adysanchez-10/Grupo-4-oficial/Documentacion/Talleres/Taller 22.10.25/Ejemplo 3/Laminado de objetos.pdf

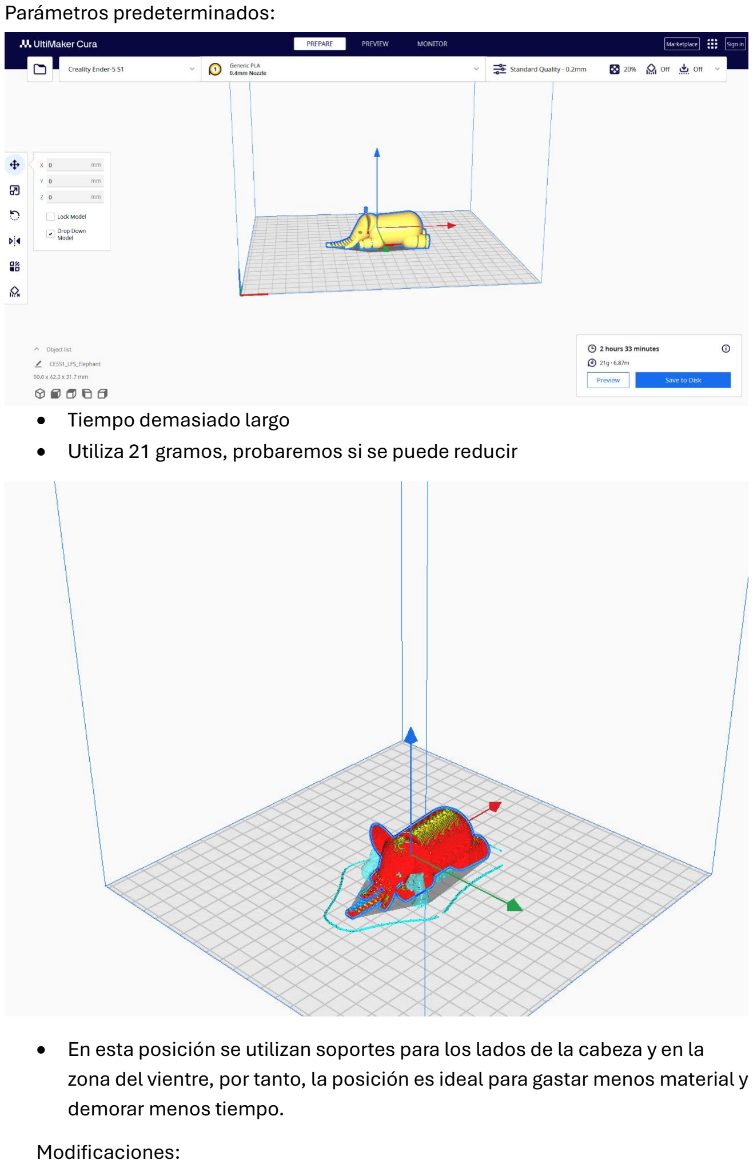
[picture p42: page 1]

Parámetros predeterminados:

- Tiempo demasiado largo
- Utiliza 21 gramos, probaremos si se puede reducir
- En esta posición se utilizan soportes para los lados de la cabeza y en la zona del vientre, por tanto, la posición es ideal para gastar menos material y demorar menos tiempo.
Modificaciones:

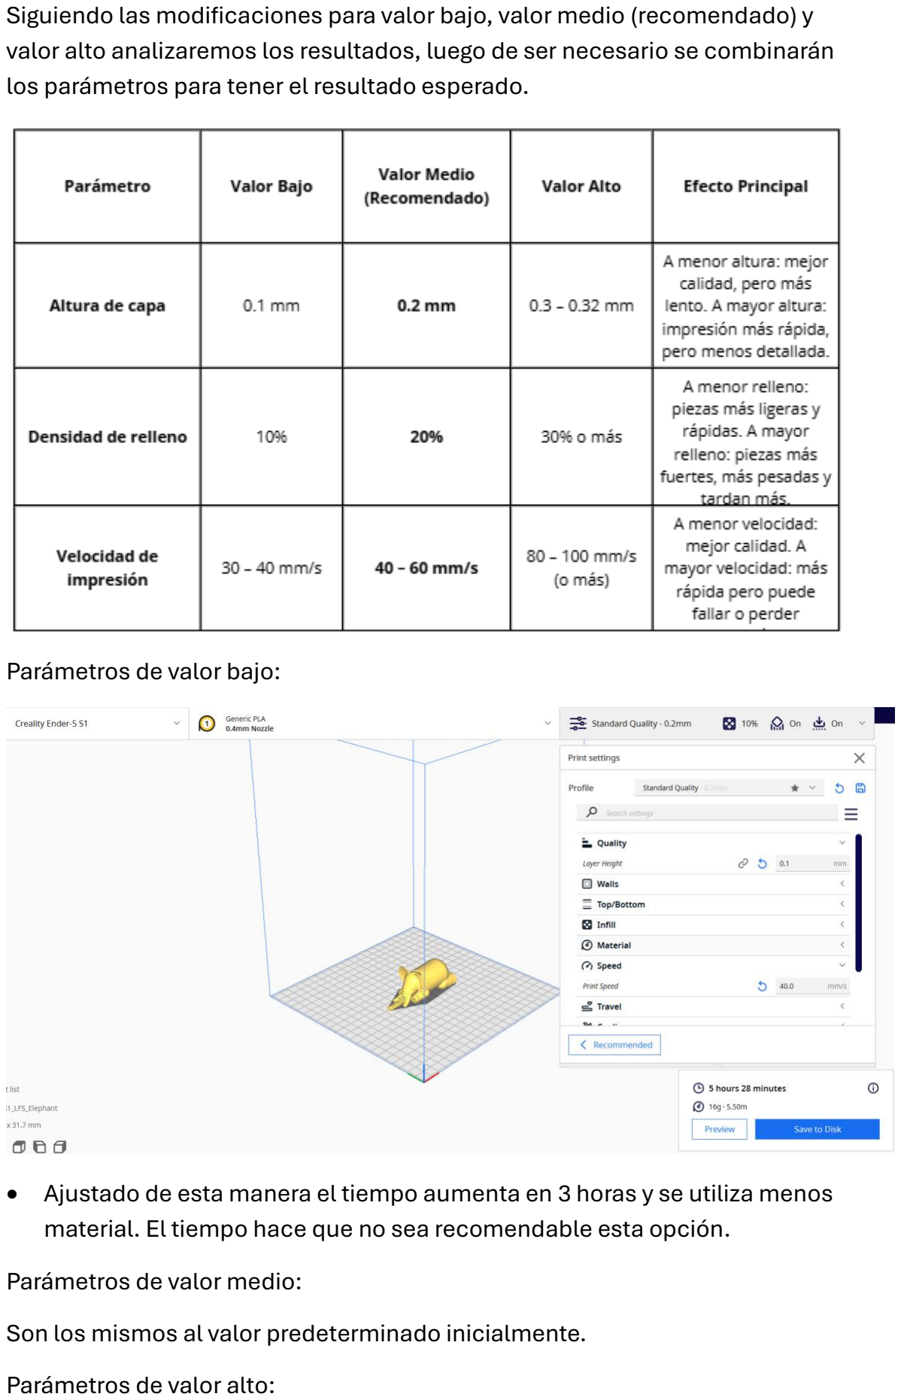
[picture p43: page 2]

Siguiendo las modificaciones para valor bajo, valor medio (recomendado) y valor alto analizaremos los resultados, luego de ser necesario se combinarán los parámetros para tener el resultado esperado.

Parámetros de valor bajo:

- Ajustado de esta manera el tiempo aumenta en 3 horas y se utiliza menos material. El tiempo hace que no sea recomendable esta opción. Parámetros de valor medio:
Son los mismos al valor predeterminado inicialmente.
Parámetros de valor alto:

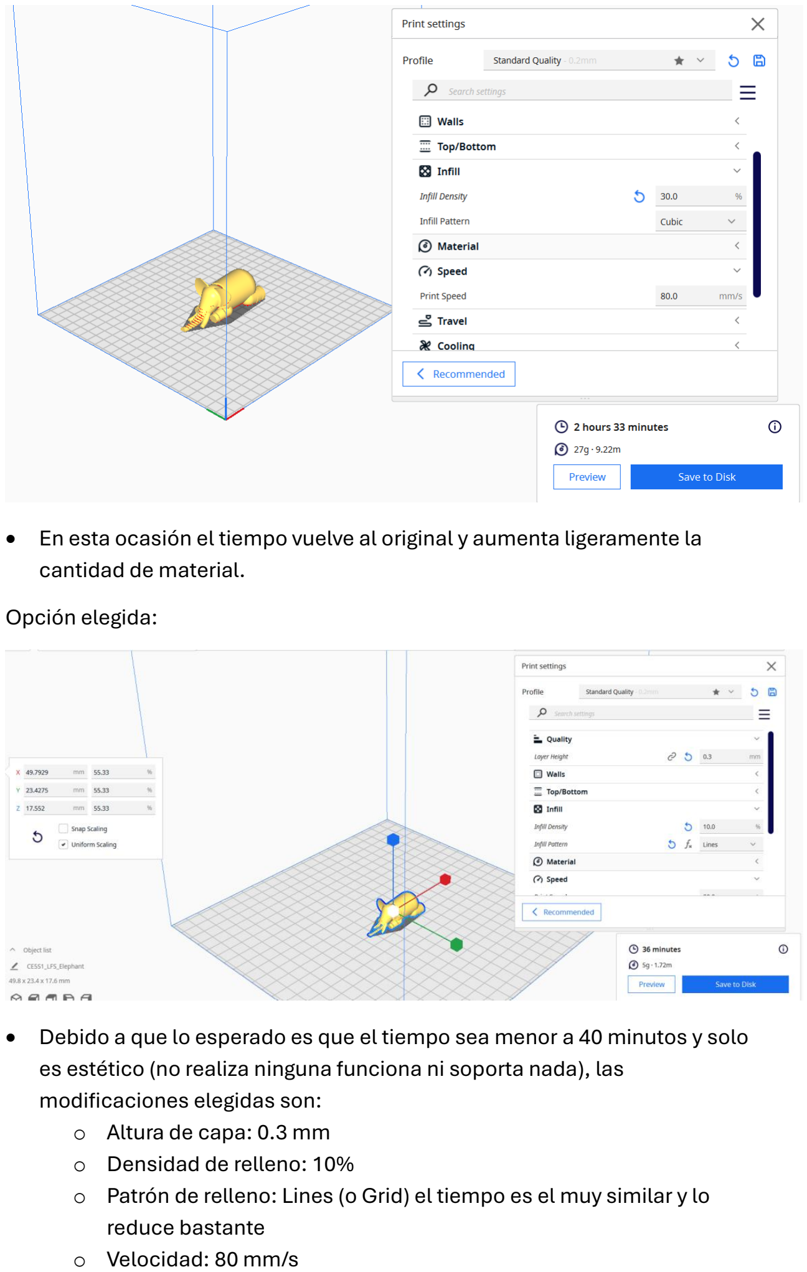
[picture p44: page 3]

- En esta ocasión el tiempo vuelve al original y aumenta ligeramente la cantidad de material.
Opción elegida:
- Debido a que lo esperado es que el tiempo sea menor a 40 minutos y solo es estético (no realiza ninguna funciona ni soporta nada), las modificaciones elegidas son:
- Altura de capa: 0.3 mm
- Densidad de relleno: 10%
- Patrón de relleno: Lines (o Grid) el tiempo es el muy similar y lo reduce bastante
- Velocidad: 80 mm/s

- Reducción de medidas: 49.8x23.4x17.6 mm (necesario para reducir el tiempo)
