adysanchez-10/Grupo-4-oficial/Documentacion/Entregables/Entregables corregidos/Entregable 8/ENTREGABLE 8 FUNBIO (1) (1).pdf

"Año de la recuperación y consolidación de la economía peruana"

## Universidad Peruana Cayetano Heredia - Pontificia Universidad Católica del Perú


## Facultad De Ciencias E Ingeniería Ingeniería Biomédica

Octavo entregable
“Diseño esquemático y modelado 3D”

Integrantes:
Rodriguéz Solano, Milagros Mariajosé Romaní León, Leonardo
Romero Guerrero, Gabriel
Salas Cano, Rodrigo Emiliano Sánchez Guevara, Ady Sebastián Seijas Rojas, Camila Andrea

Cuarto ciclo
Profesores:
Miguel Rogger Hoyos Alvitez Marco Mugaburu Celi
Shirley Pahuachon Nuñez
Fecha de entrega: 21/10/2025

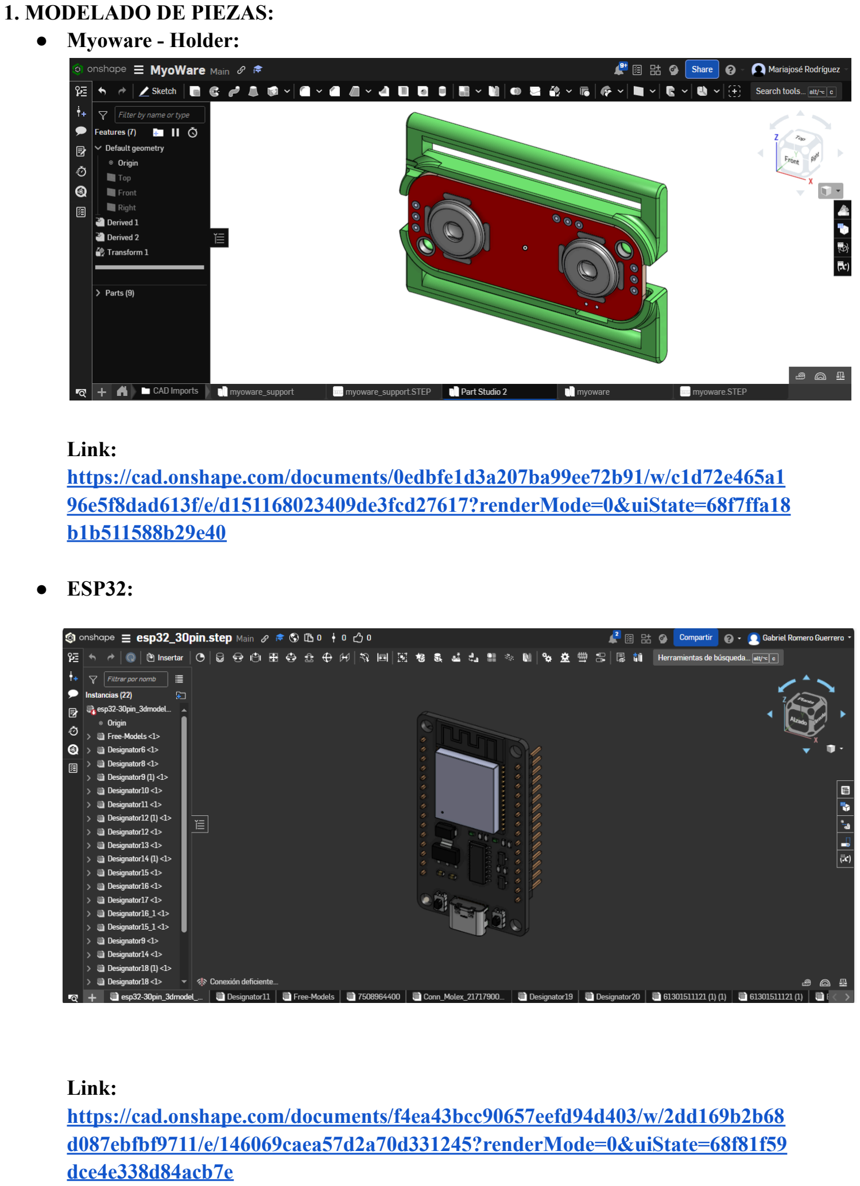
[picture p45: page 2]

### 1. MODELADO DE PIEZAS:

- Myoware - Holder:

Link:
https://cad.onshape.com/documents/0edbfe1d3a207ba99ee72b91/w/c1d72e465a196e5f8dad613f/e/d151168023409de3fcd27617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 b1b511588b29e40 (https://cad.onshape.com/documents/0edbfe1d3a207ba99ee72b91/w/c1d72e465a196e5f8dad613f/e/d151168023409de3fcd27617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)
- ESP32:

Link:
https://cad.onshape.com/documents/f4ea43bcc90657eefd94d403/w/2dd169b2b68d087ebfbf9711/e/146069caea57d2a70d331245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 dce4e338d84acb7e (https://cad.onshape.com/documents/f4ea43bcc90657eefd94d403/w/2dd169b2b68d087ebfbf9711/e/146069caea57d2a70d331245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)

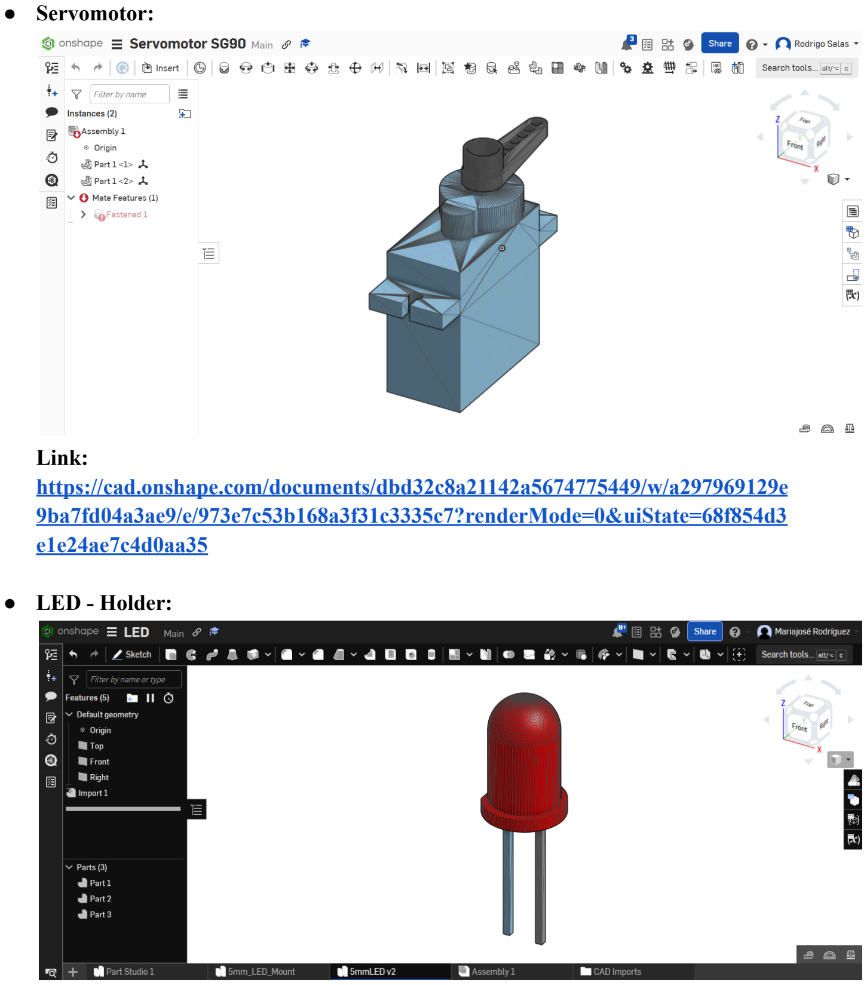
[picture p46: page 3]

- Servomotor:

Link:
https://cad.onshape.com/documents/dbd32c8a21142a5674775449/w/a297969129e9ba7fd04a3ae9/e/973e7c53b168a3f31c3335c7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 e1e24ae7c4d0aa35 (https://cad.onshape.com/documents/dbd32c8a21142a5674775449/w/a297969129e9ba7fd04a3ae9/e/973e7c53b168a3f31c3335c7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)
- LED - Holder:

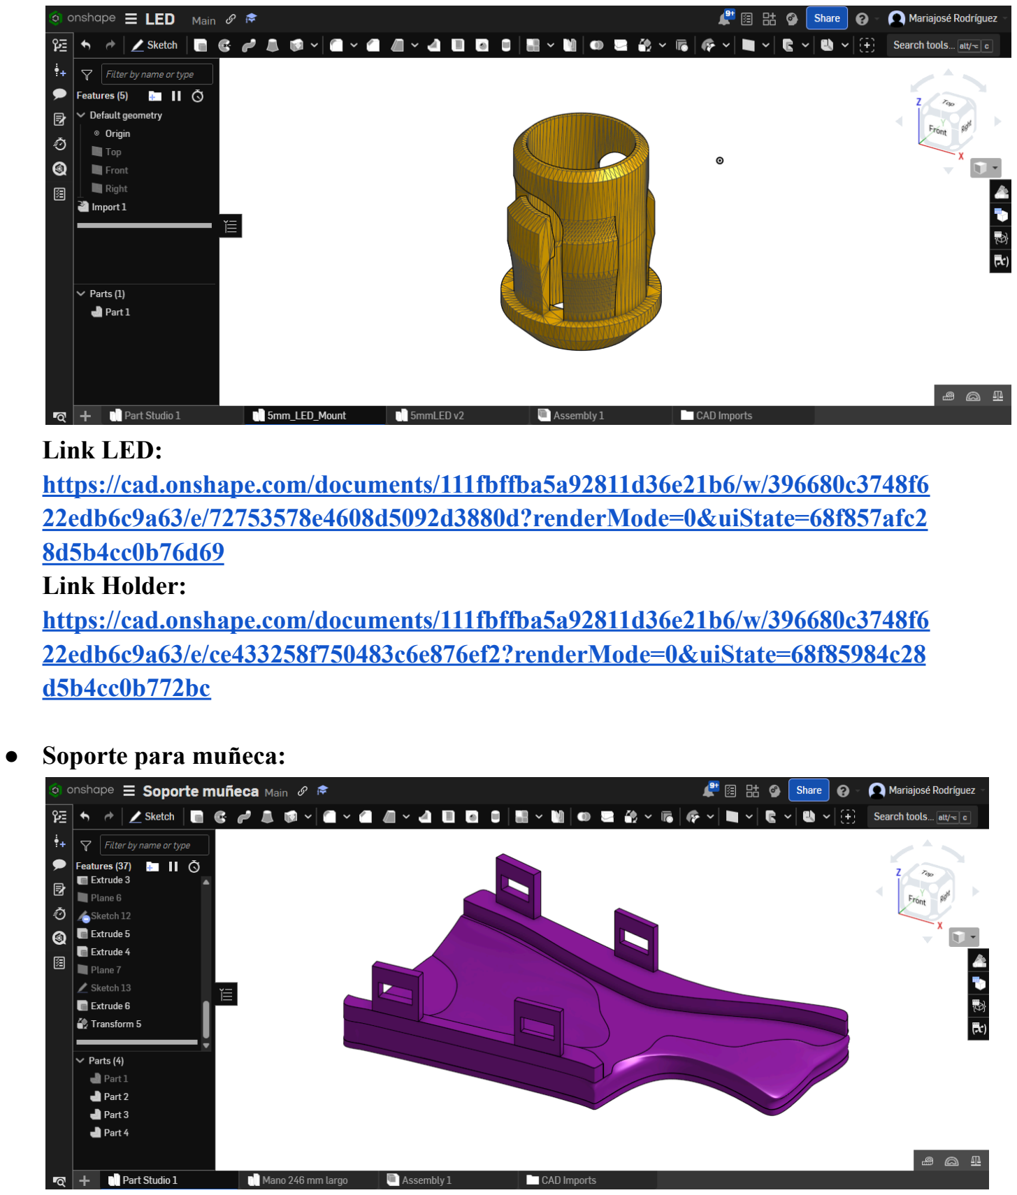
[picture p47: page 4]

Link LED:
https://cad.onshape.com/documents/111fbffba5a92811d36e21b6/w/396680c3748f622edb6c9a63/e/72753578e4608d5092d3880d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 8d5b4cc0b76d69 (https://cad.onshape.com/documents/111fbffba5a92811d36e21b6/w/396680c3748f622edb6c9a63/e/72753578e4608d5092d3880d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)
Link Holder:
https://cad.onshape.com/documents/111fbffba5a92811d36e21b6/w/396680c3748f622edb6c9a63/e/ce433258f750483c6e876ef2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 d5b4cc0b772bc (https://cad.onshape.com/documents/111fbffba5a92811d36e21b6/w/396680c3748f622edb6c9a63/e/ce433258f750483c6e876ef2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)
- Soporte para muñeca:

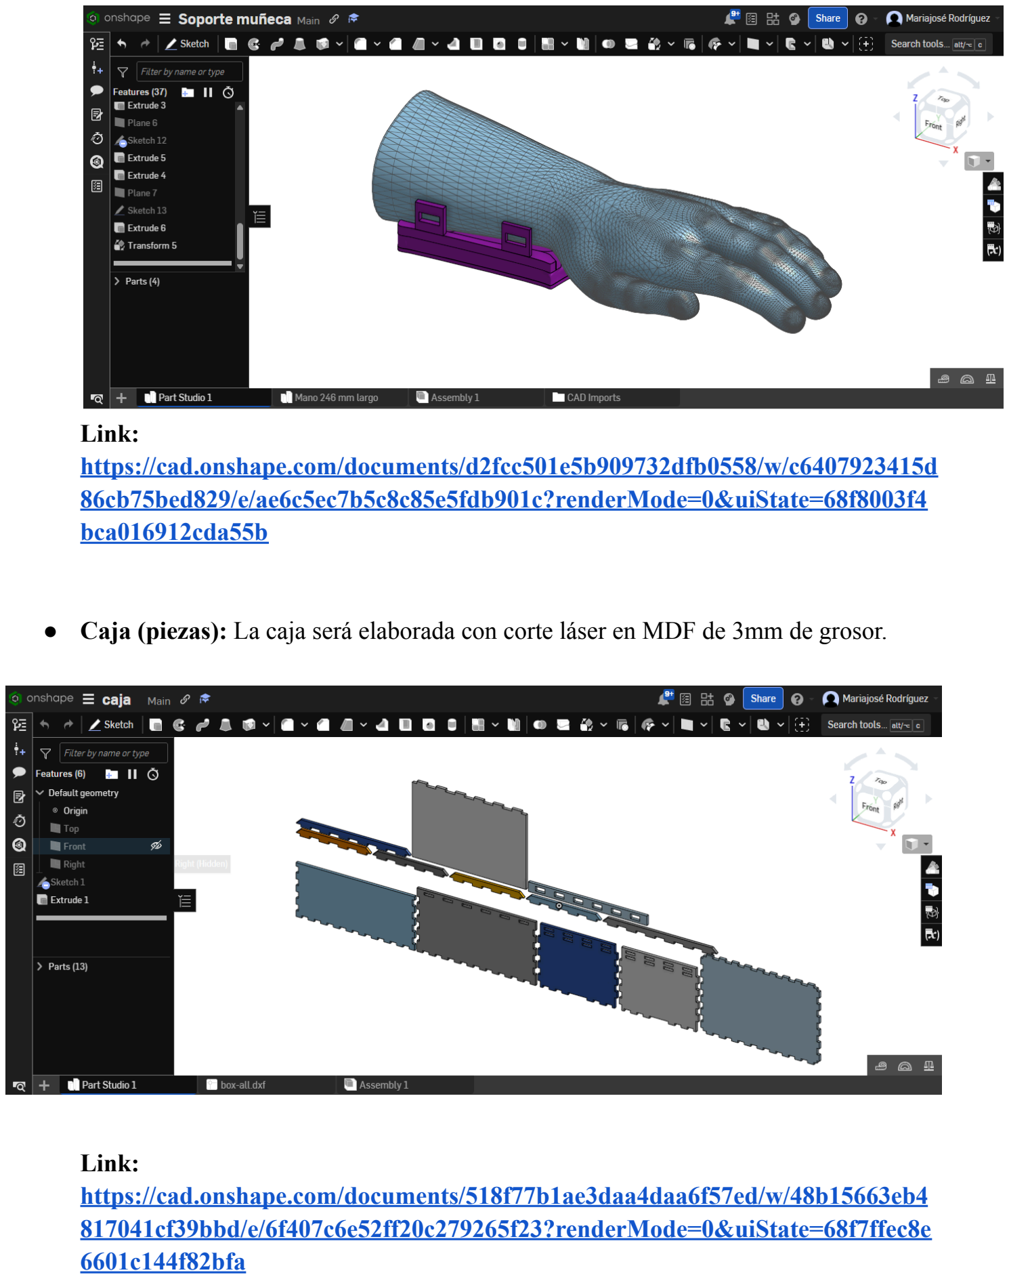
[picture p48: page 5]

Link:
https://cad.onshape.com/documents/d2fcc501e5b909732dfb0558/w/c6407923415d86cb75bed829/e/ae6c5ec7b5c8c85e5fdb901c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 bca016912cda55b (https://cad.onshape.com/documents/d2fcc501e5b909732dfb0558/w/c6407923415d86cb75bed829/e/ae6c5ec7b5c8c85e5fdb901c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)
- Caja (piezas): La caja será elaborada con corte láser en MDF de 3mm de grosor.

Link:
https://cad.onshape.com/documents/518f77b1ae3daa4daa6f57ed/w/48b15663eb4817041cf39bbd/e/6f407c6e52ff20c279265f23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 6601c144f82bfa (https://cad.onshape.com/documents/518f77b1ae3daa4daa6f57ed/w/48b15663eb4817041cf39bbd/e/6f407c6e52ff20c279265f23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)

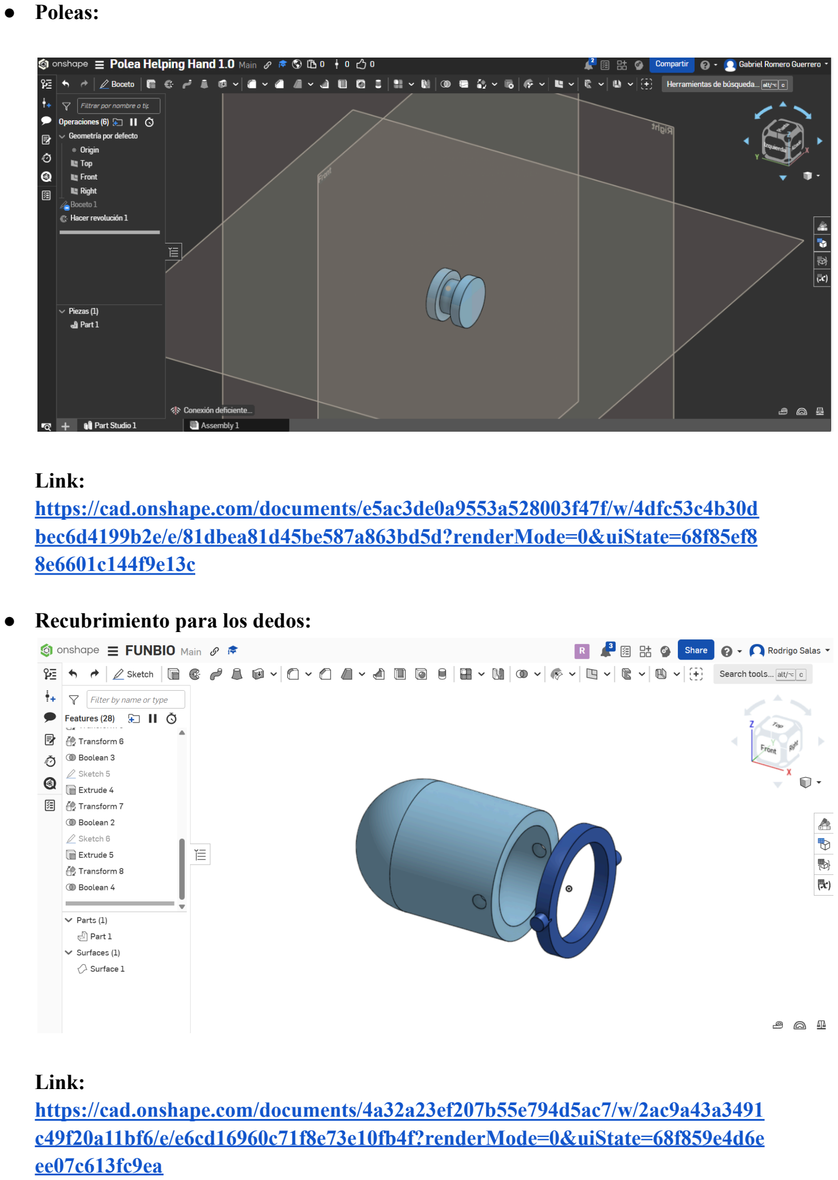
[picture p49: page 6]

- Poleas:

Link:
https://cad.onshape.com/documents/e5ac3de0a9553a528003f47f/w/4dfc53c4b30dbec6d4199b2e/e/81dbea81d45be587a863bd5d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 8e6601c144f9e13c (https://cad.onshape.com/documents/e5ac3de0a9553a528003f47f/w/4dfc53c4b30dbec6d4199b2e/e/81dbea81d45be587a863bd5d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)
- Recubrimiento para los dedos:

Link:
https://cad.onshape.com/documents/4a32a23ef207b55e794d5ac7/w/2ac9a43a3491c49f20a11bf6/e/e6cd16960c71f8e73e10fb4f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 ee07c613fc9ea (https://cad.onshape.com/documents/4a32a23ef207b55e794d5ac7/w/2ac9a43a3491c49f20a11bf6/e/e6cd16960c71f8e73e10fb4f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)

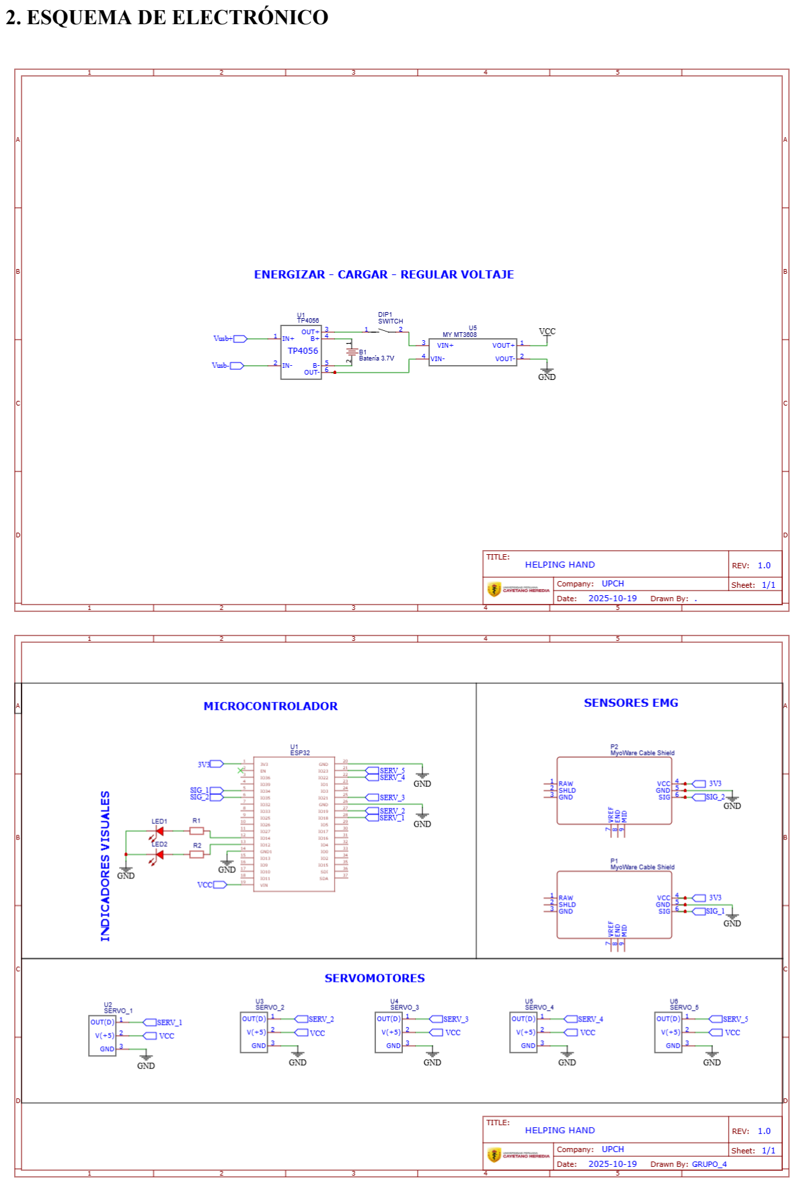
[picture p50: page 7]

### 2. ESQUEMA DE ELECTRÓNICO
