adysanchez-10/Grupo-4-oficial/Documentacion/Talleres/Taller 5 Modelado 3D/Ady Sánchez/ady-sebastian-snchez-guevara-d6649073-1fdc-455c-b664-97311cb8ef63-certificate.pdf

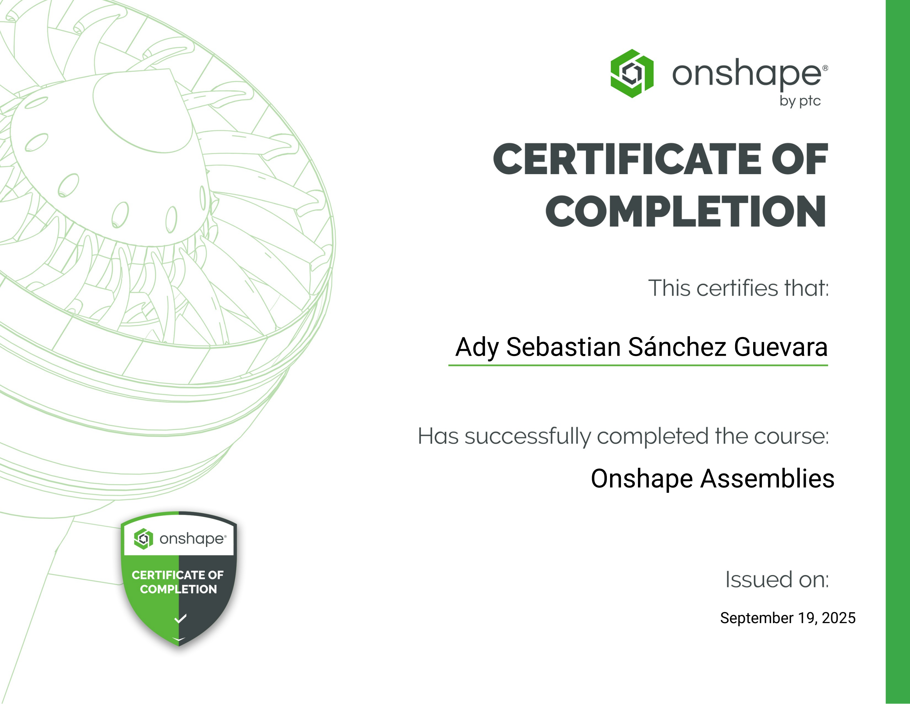
[picture p59: page 1]

Ady Sebastian Sánchez Guevara

September 19, 2025

Onshape Assemblies
