adysanchez-10/Grupo-4-oficial/Documentacion/Talleres/Taller 5 Modelado 3D/Leonardo Romaní/leonardo-romani-9ebd93d2-e420-4a95-a075-f9c7511aa4ec-certificate.pdf

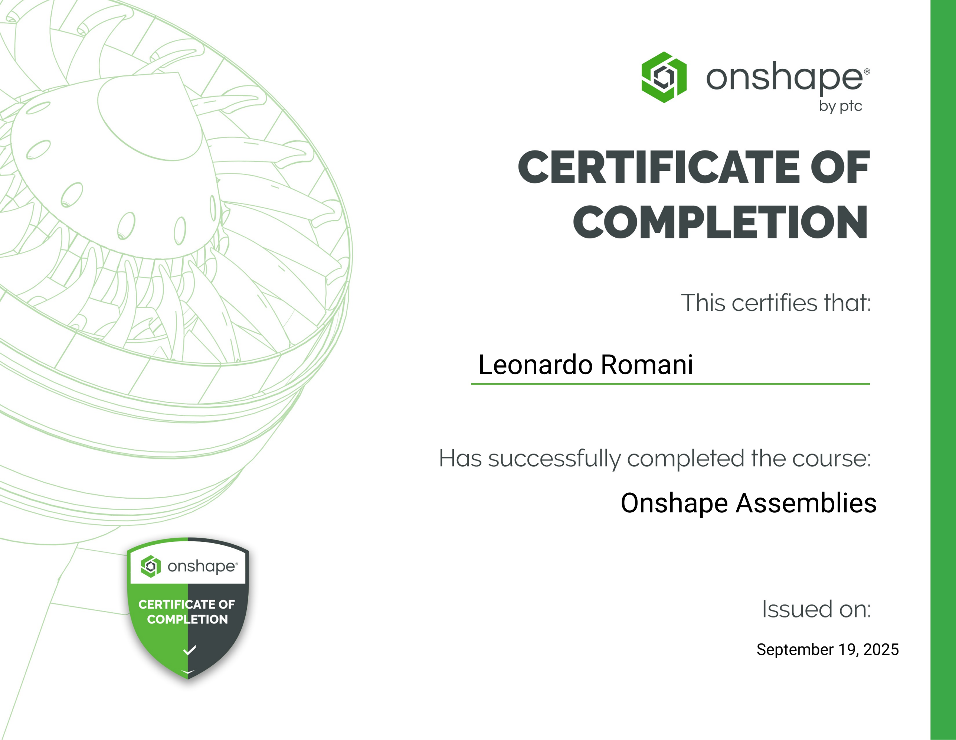
[picture p60: page 1]

Leonardo Romani

September 19, 2025

Onshape Assemblies
