adysanchez-10/Grupo-4-oficial/Documentacion/Talleres/Taller 5 Modelado 3D/Camila Seijas Rojas/Detailed Drawings.pdf

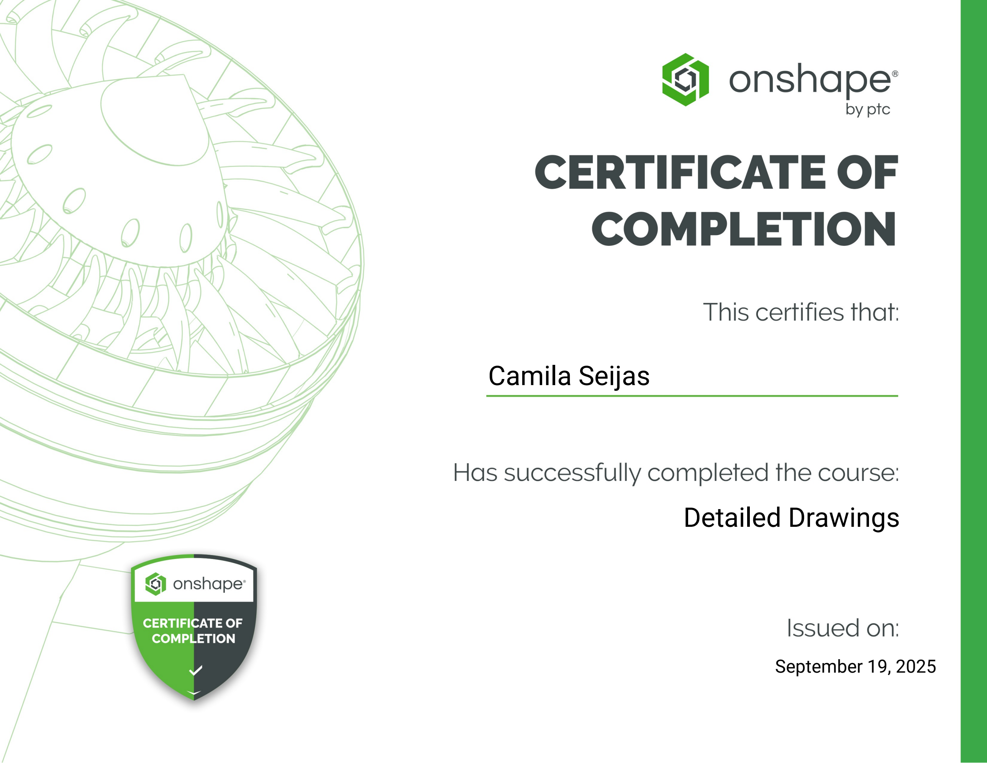
[picture p116: page 1]

Camila Seijas

September 19, 2025

Detailed Drawings
