adysanchez-10/Grupo-4-oficial/Documentacion/Talleres/Taller 5 Modelado 3D/Camila Seijas Rojas/Introduction to Part Studios.pdf

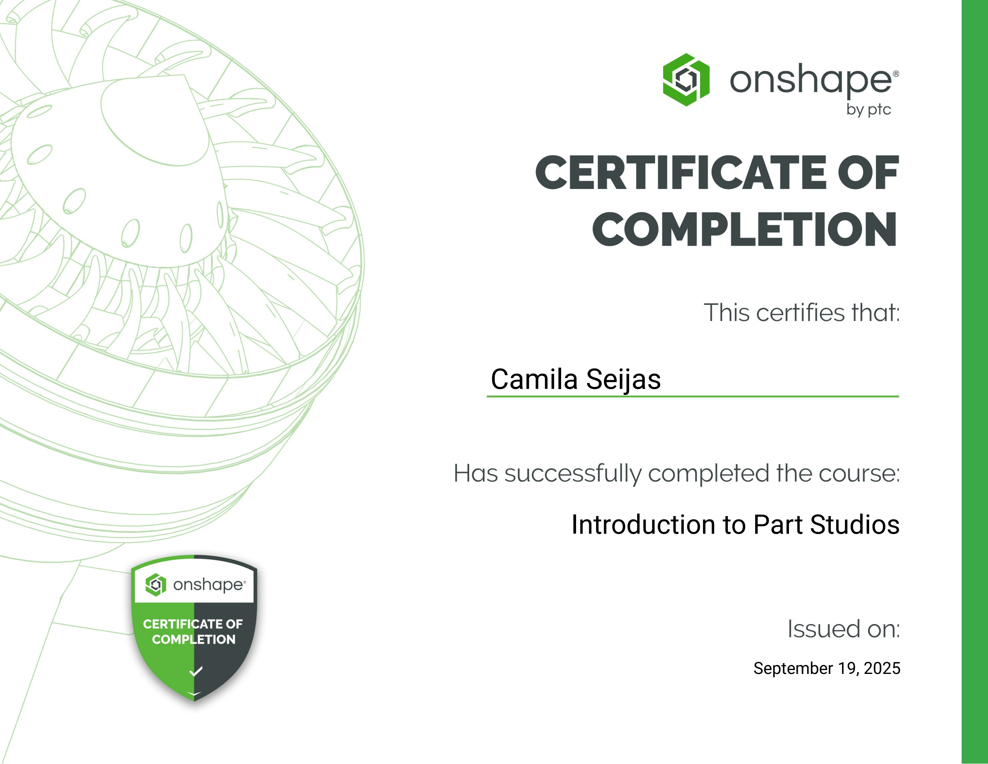
[picture p117: page 1]

Camila Seijas

Introduction to Part Studios

September 19, 2025
