adysanchez-10/Grupo-4-oficial/Documentacion/Talleres/Taller 5 Modelado 3D/Camila Seijas Rojas/Introduction to Sketching.pdf

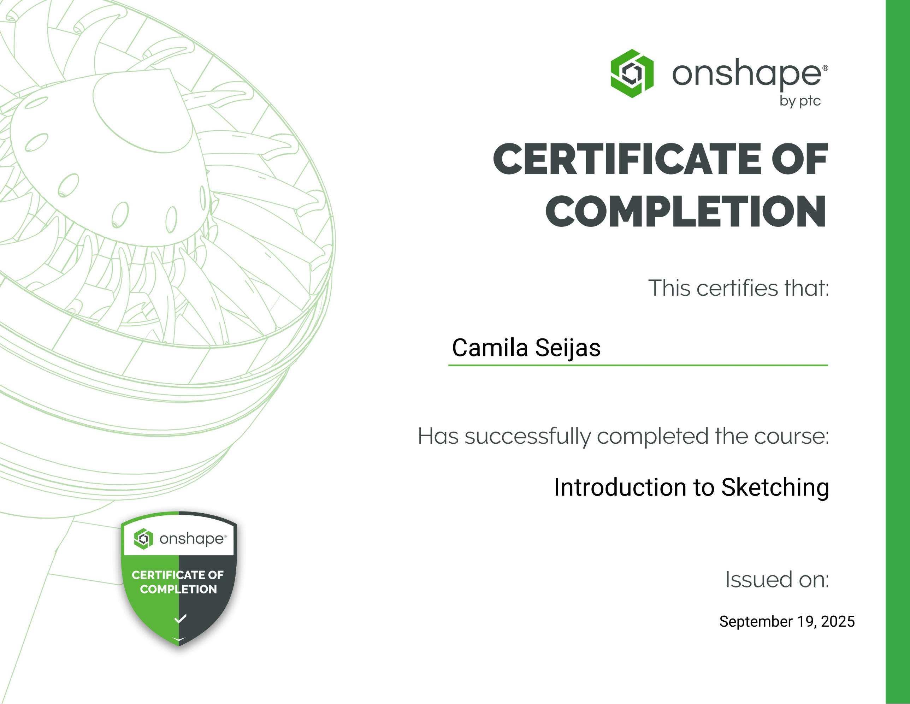
[picture p118: page 1]

Camila Seijas

Introduction to Sketching

September 19, 2025
