adysanchez-10/Grupo-4-oficial/Documentacion/Talleres/Taller 5 Modelado 3D/Camila Seijas Rojas/Multi-Part Part Studios.pdf

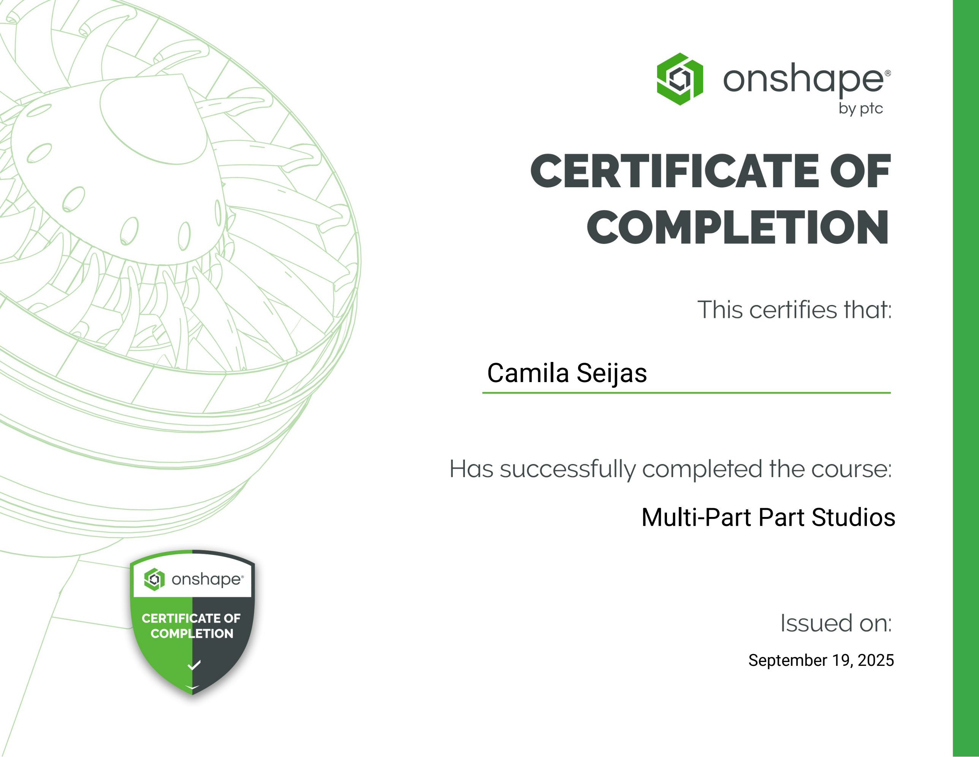
[picture p119: page 1]

Camila Seijas

September 19, 2025

Multi-Part Part Studios
