adysanchez-10/Grupo-4-oficial/Documentacion/Talleres/Taller 5 Modelado 3D/Milagros Mariajosé Rodríguez Solano/Introduction to Sketching.pdf

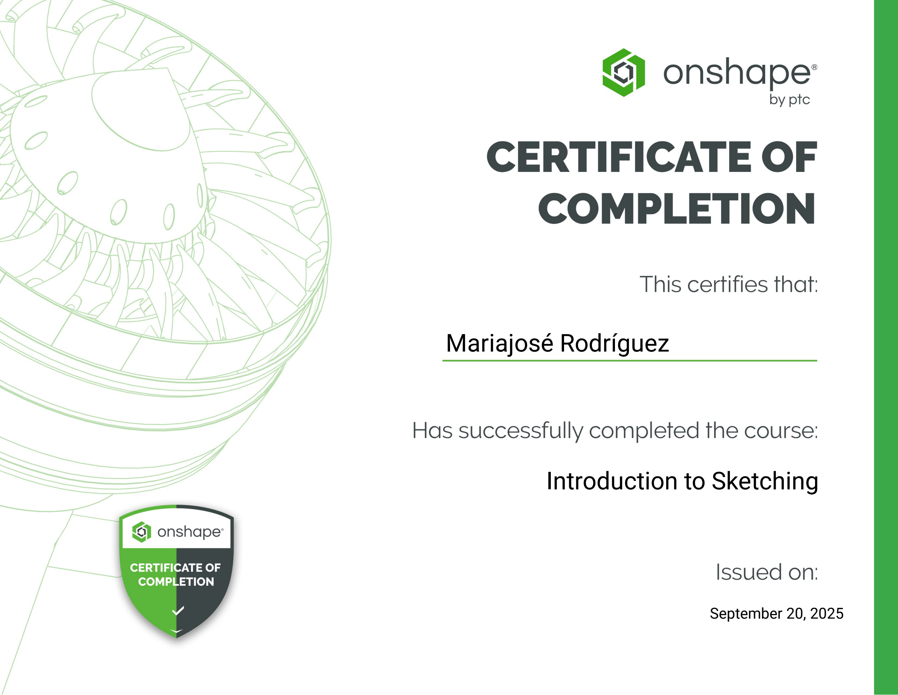
[picture p121: page 1]

Mariajosé Rodríguez

Introduction to Sketching

September 20, 2025
