adysanchez-10/Grupo-4-oficial/Documentacion/Talleres/Taller 5 Modelado 3D/Milagros Mariajosé Rodríguez Solano/Multi-Part Part Studios.pdf

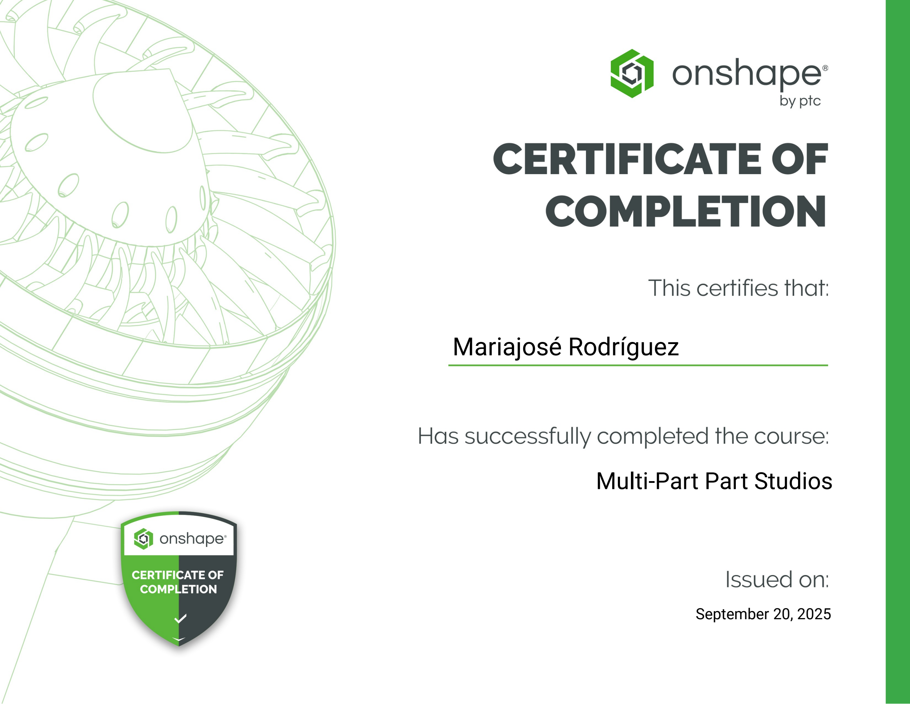
[picture p122: page 1]

Mariajosé Rodríguez

September 20, 2025

Multi-Part Part Studios
