adysanchez-10/Grupo-4-oficial/Documentacion/Talleres/Taller 5 Modelado 3D/Milagros Mariajosé Rodríguez Solano/Part Studios.pdf

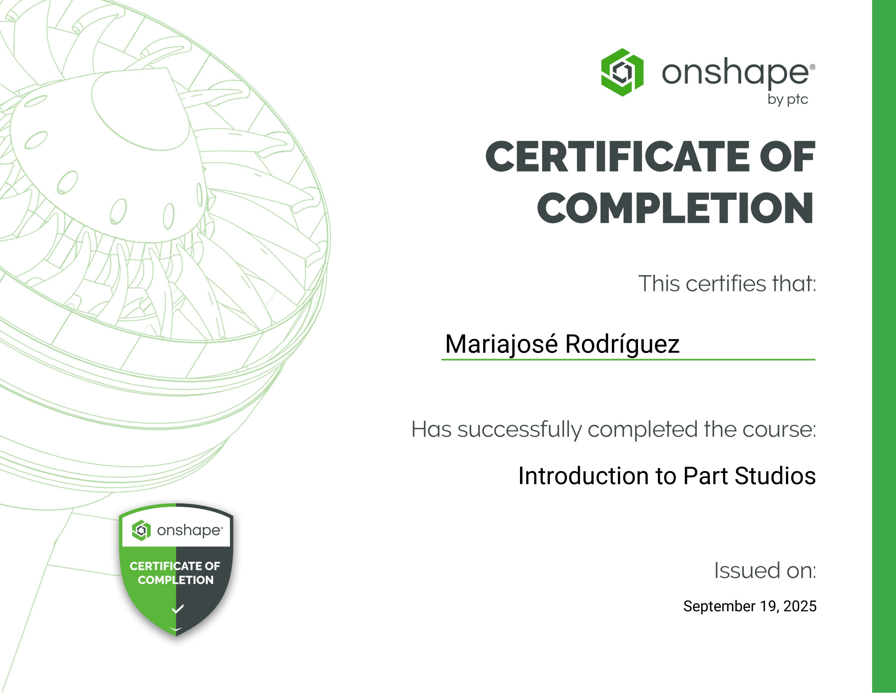
[picture p123: page 1]

Mariajosé Rodríguez

Introduction to Part Studios

September 19, 2025
