adysanchez-10/Grupo-4-oficial/Documentacion/Talleres/Taller 5 Modelado 3D/Ady Sánchez/ady-sebastian-snchez-guevara-8aa23c59-1baa-40a5-9c81-66c02d83bc40-certificate.pdf

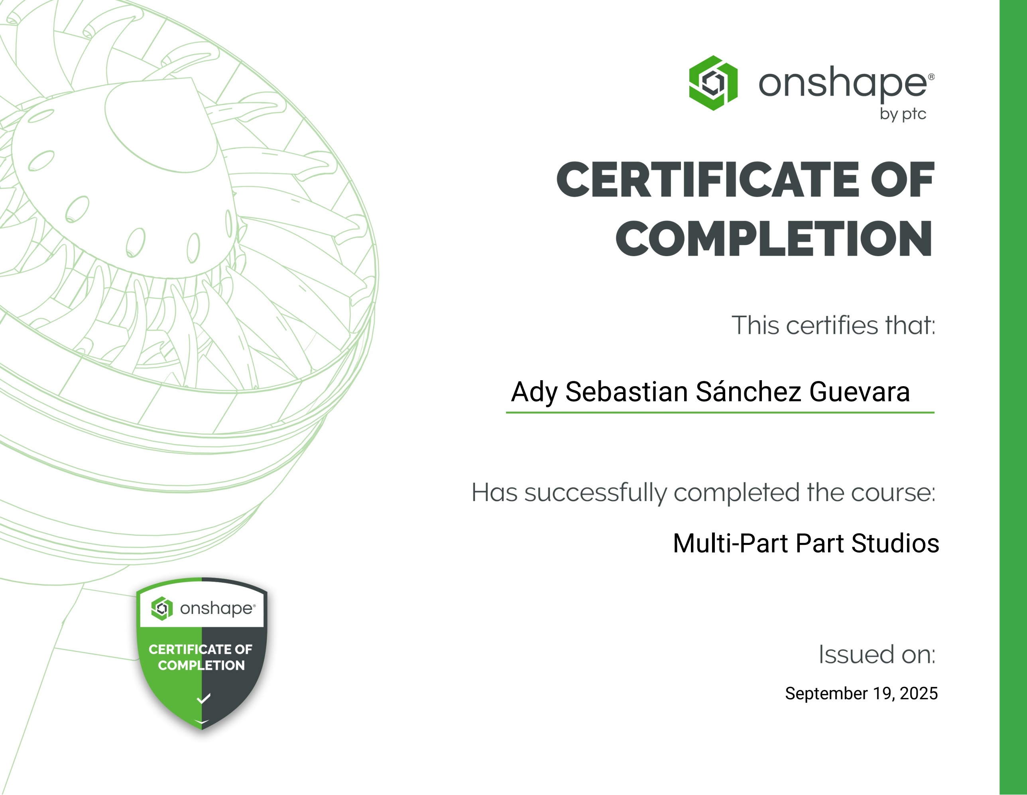
[picture p124: page 1]

Ady Sebastian Sánchez Guevara

September 19, 2025

Multi-Part Part Studios
