adysanchez-10/Grupo-4-oficial/Documentacion/Talleres/Taller 5 Modelado 3D/Ady Sánchez/ady-sebastian-snchez-guevara-c8a2fdc6-5e11-4440-b1be-523359297e63-certificate.pdf

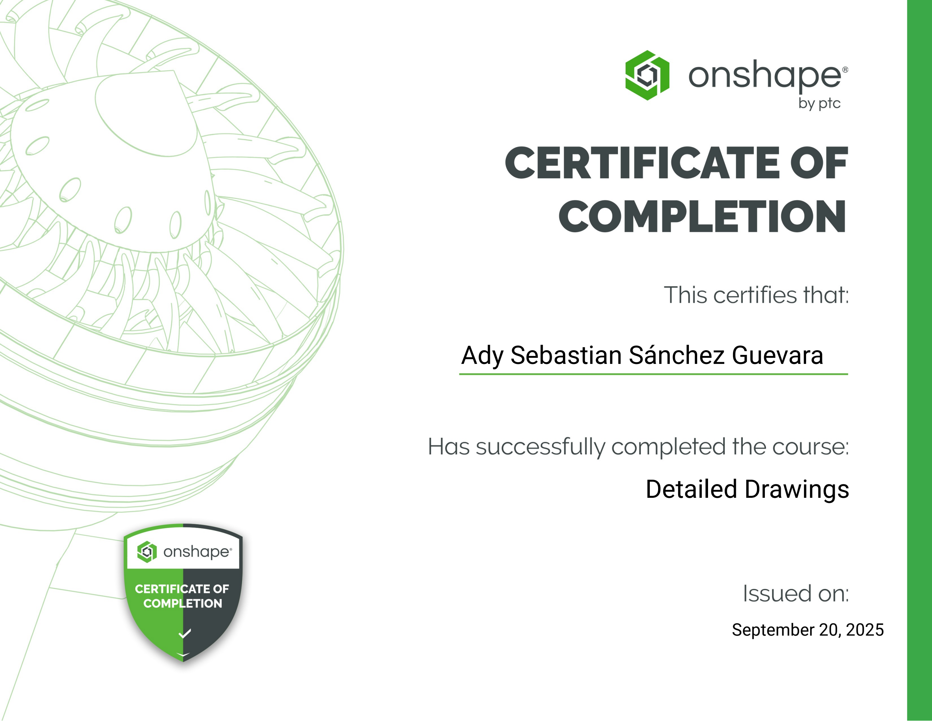
[picture p125: page 1]

Ady Sebastian Sánchez Guevara

September 20, 2025

Detailed Drawings
