adysanchez-10/Grupo-4-oficial/Documentacion/Talleres/Taller 5 Modelado 3D/Ady Sánchez/ady-sebastian-snchez-guevara-d0e903c4-ef2c-4c85-911b-dd67b3c3be91-certificate.pdf

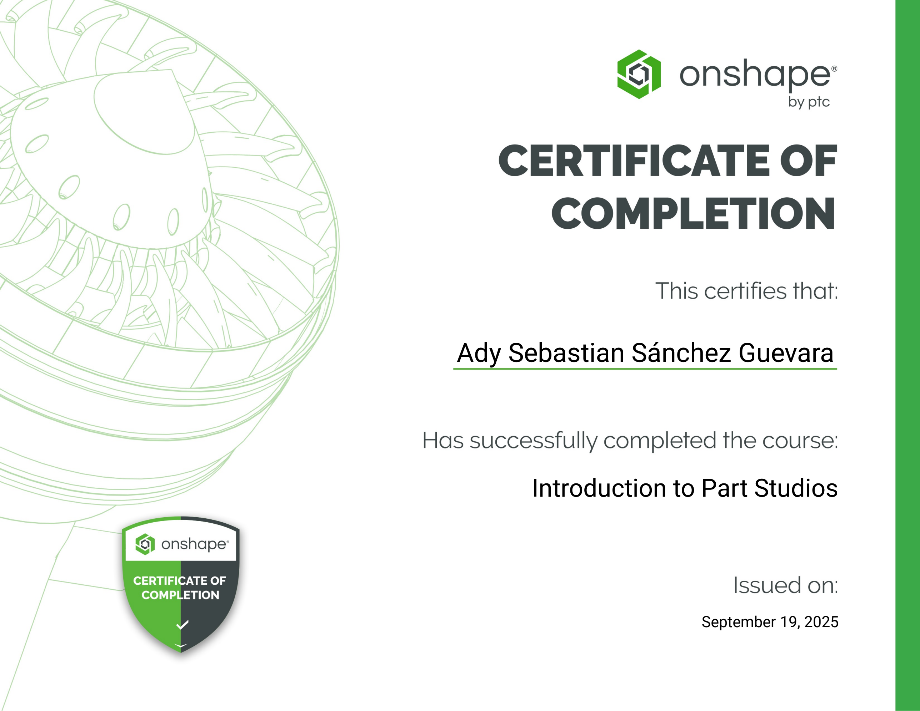
[picture p126: page 1]

Ady Sebastian Sánchez Guevara

Introduction to Part Studios

September 19, 2025
