adysanchez-10/Grupo-4-oficial/Documentacion/Talleres/Taller 5 Modelado 3D/Ady Sánchez/ady-sebastian-snchez-guevara-e92367d2-3b48-4529-b158-4c80df272a35-certificate.pdf

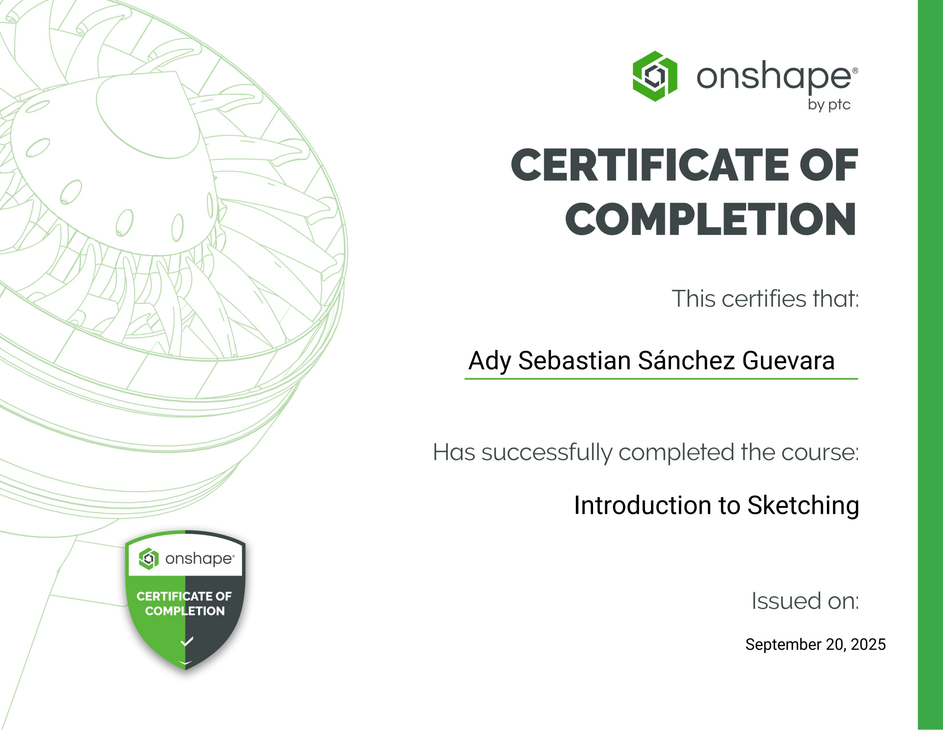
[picture p127: page 1]

Ady Sebastian Sánchez Guevara

Introduction to Sketching

September 20, 2025
