adysanchez-10/Grupo-4-oficial/Documentacion/Talleres/Taller 5 Modelado 3D/Leonardo Romaní/leonardo-romani-6423bbf2-b606-4ca5-bd36-236f7cc2e1d3-certificate.pdf

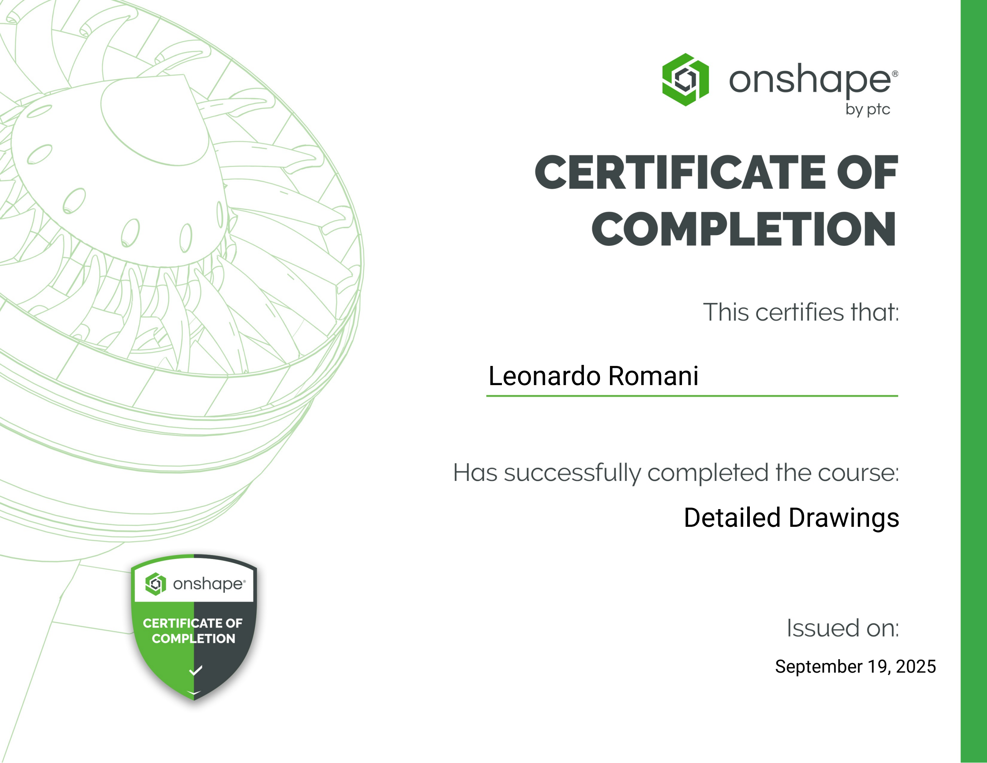
[picture p128: page 1]

Leonardo Romani

September 19, 2025

Detailed Drawings
