adysanchez-10/Grupo-4-oficial/Documentacion/Talleres/Taller 5 Modelado 3D/Leonardo Romaní/leonardo-romani-96d0b658-acae-4825-a745-9fc13c1be463-certificate.pdf

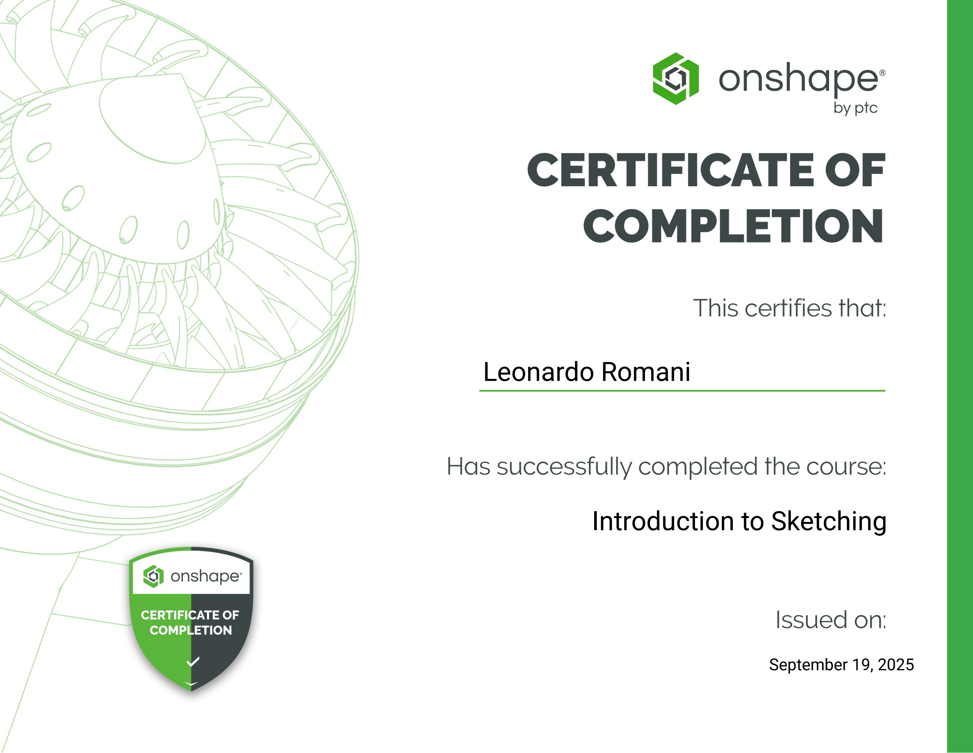
[picture p129: page 1]

Leonardo Romani

Introduction to Sketching

September 19, 2025
