adysanchez-10/Grupo-4-oficial/Documentacion/Talleres/Taller 5 Modelado 3D/Leonardo Romaní/leonardo-romani-b80795b1-2418-4cdc-8e88-4afec2bf2f4b-certificate.pdf

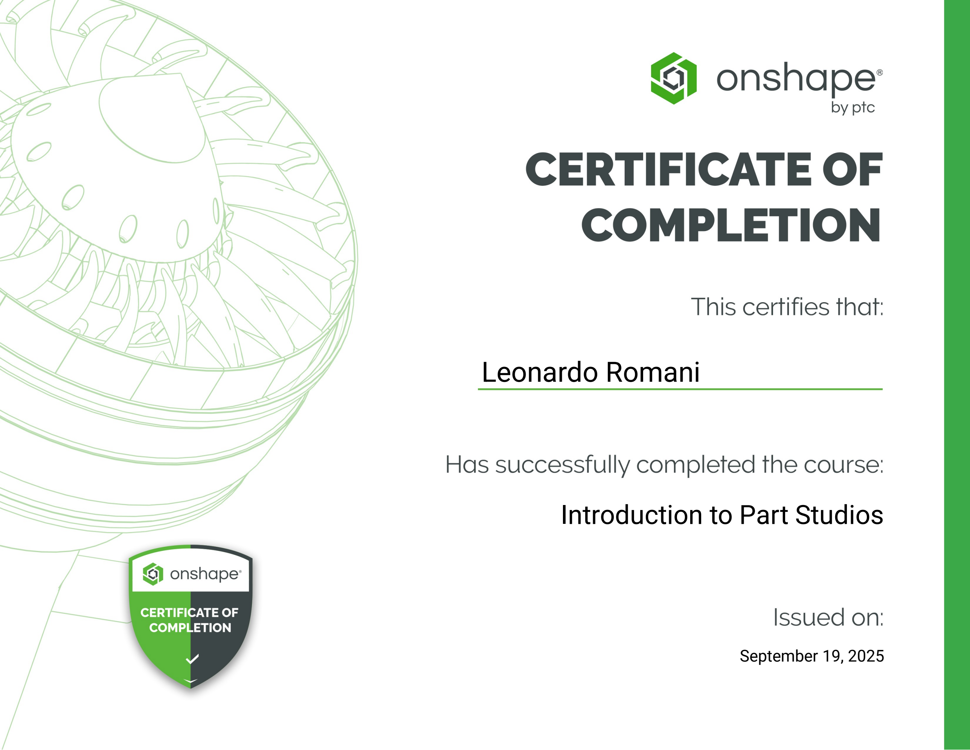
[picture p130: page 1]

Leonardo Romani

Introduction to Part Studios

September 19, 2025
