adysanchez-10/Grupo-4-oficial/Documentacion/Talleres/Taller 5 Modelado 3D/Leonardo Romaní/leonardo-romani-e20d42cd-ce88-4bdb-a8e0-e006e294c3c1-certificate.pdf

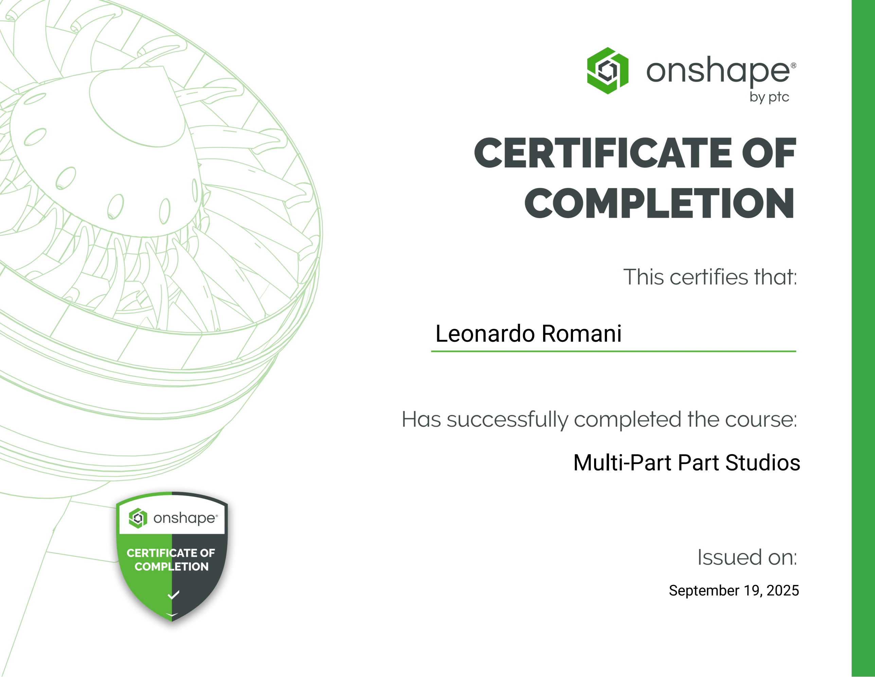
[picture p131: page 1]

Leonardo Romani

September 19, 2025

Multi-Part Part Studios
