adysanchez-10/Grupo-4-oficial/Documentacion/Talleres/Taller 02.10.25/Proyecto 1/APP.jpg

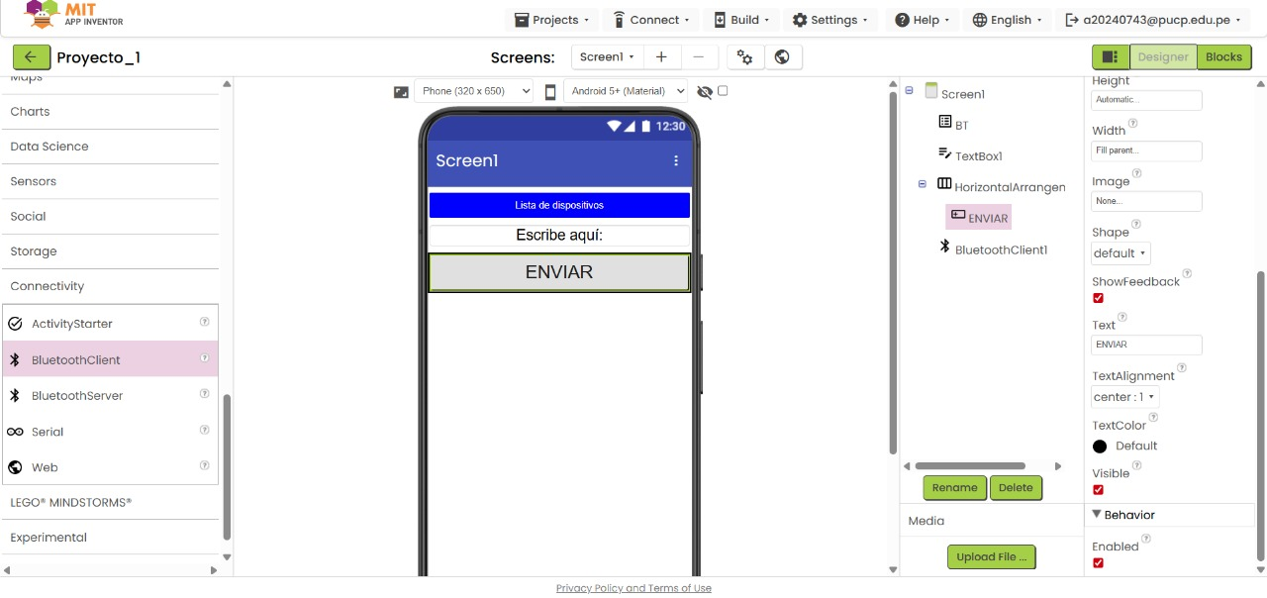
Documentacion/Talleres/Taller 02.10.25/Proyecto 1/APP.jpg
