adysanchez-10/Grupo-4-oficial/Documentacion/Talleres/Taller 02.10.25/Proyecto 1/Captura de pantalla 2025-10-04 162429.png

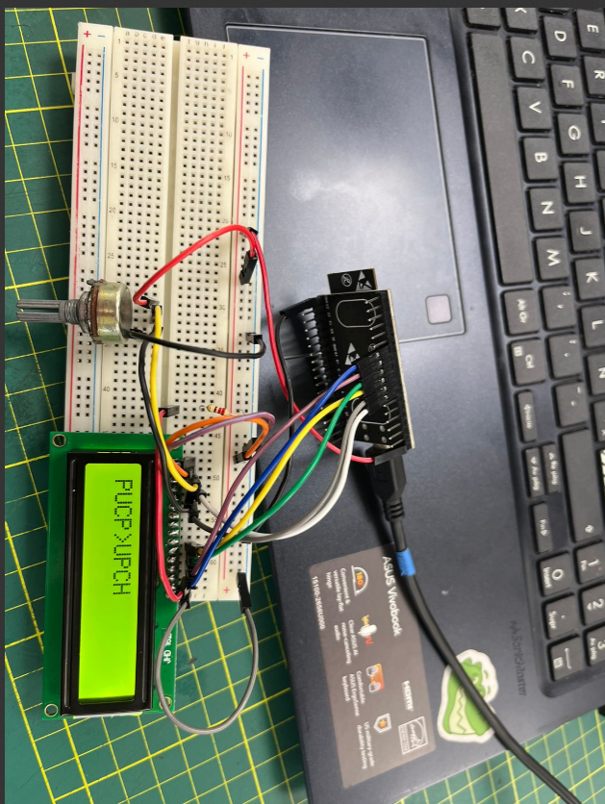
Documentacion/Talleres/Taller 02.10.25/Proyecto 1/Captura de pantalla 2025-10-04 162429.png
