adysanchez-10/Grupo-4-oficial/Documentacion/Talleres/Taller 02.10.25/Proyecto 2/p1.jpg

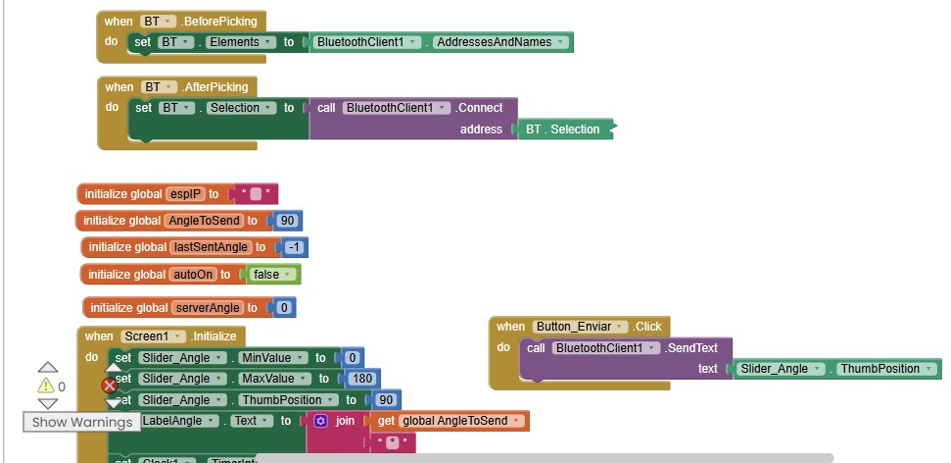
Documentacion/Talleres/Taller 02.10.25/Proyecto 2/p1.jpg
