adysanchez-10/Grupo-4-oficial/Documentacion/Talleres/Taller 5 Modelado 3D/Ady Sánchez/Captura de pantalla 2025-09-19 225339.png

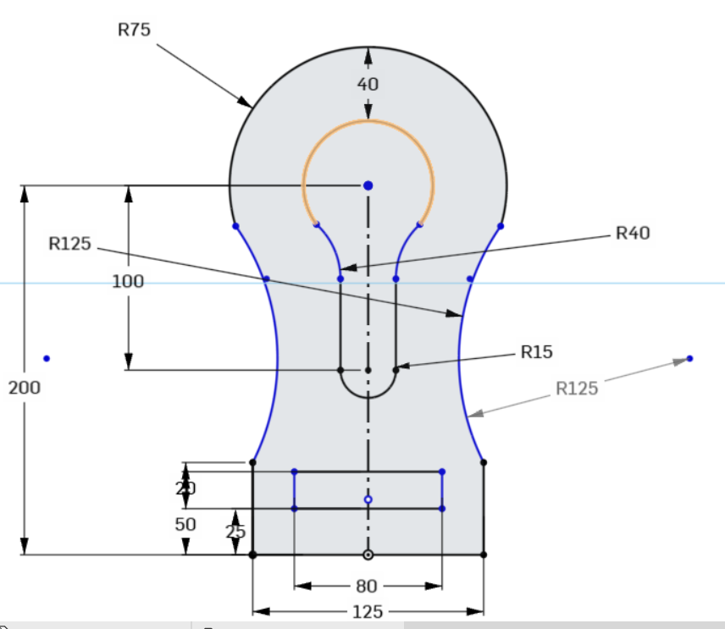
Documentacion/Talleres/Taller 5 Modelado 3D/Ady Sánchez/Captura de pantalla 2025-09-19 225339.png
