adysanchez-10/Grupo-4-oficial/Documentacion/Talleres/Taller 5 Modelado 3D/Milagros Mariajosé Rodríguez Solano/Ejercicio clase.png

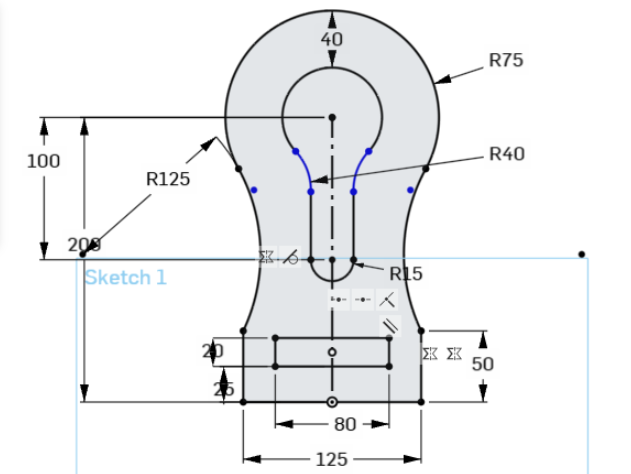
Documentacion/Talleres/Taller 5 Modelado 3D/Milagros Mariajosé Rodríguez Solano/Ejercicio clase.png
