adysanchez-10/Grupo-4-oficial/Documentacion/Talleres/Taller 22.10.25/Ejemplo 1/elefante.png

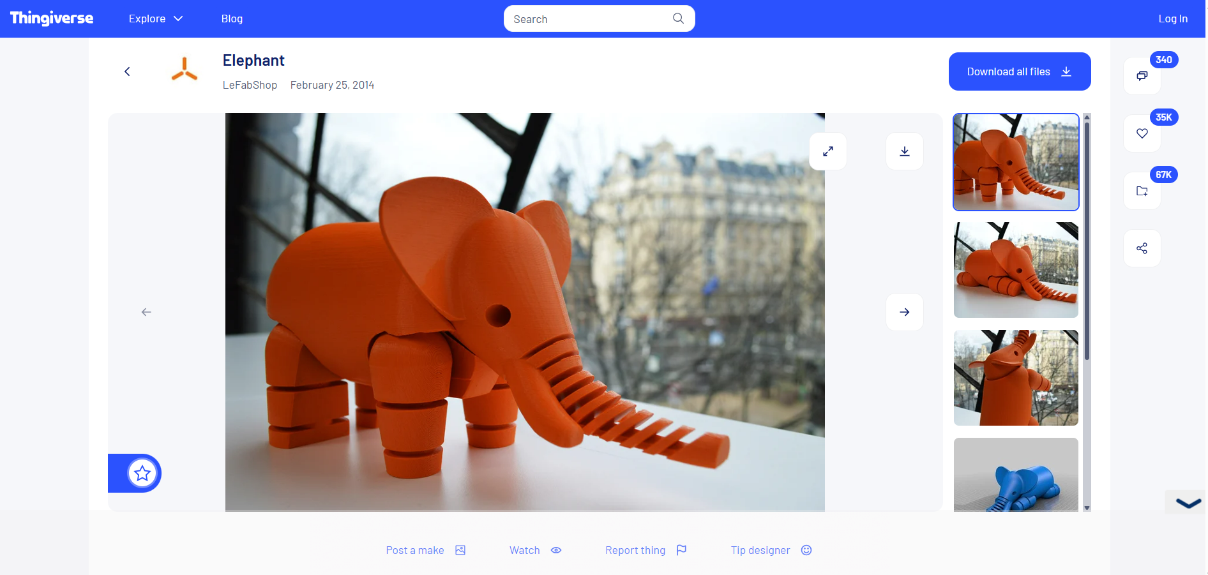
Documentacion/Talleres/Taller 22.10.25/Ejemplo 1/elefante.png
