adysanchez-10/Grupo-4-oficial/Documentacion/Talleres/Taller de electrónica/T1/T1.jpg

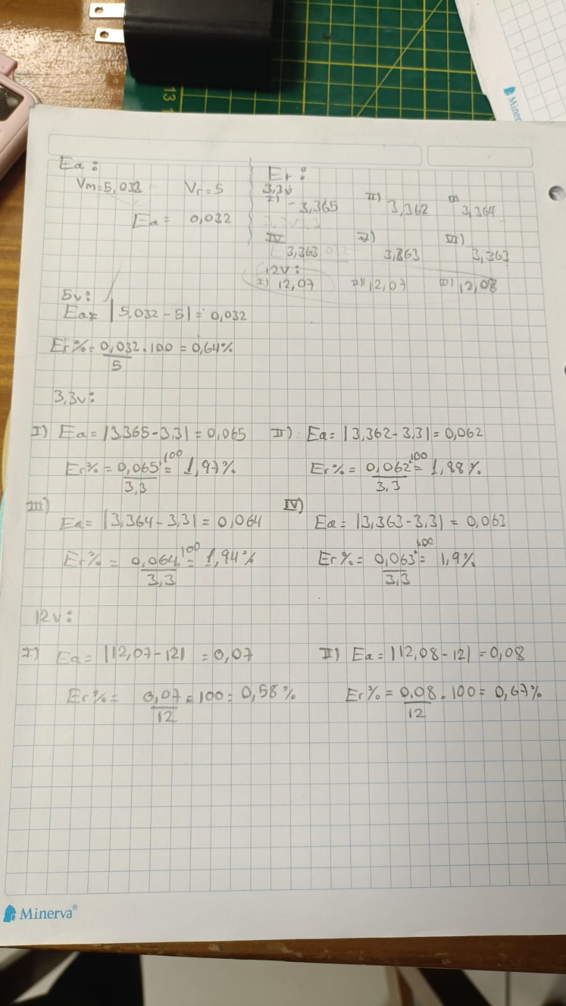
Documentacion/Talleres/Taller de electrónica/T1/T1.jpg
