adysanchez-10/Grupo-4-oficial/Documentacion/Talleres/Taller de electrónica/T2/pollo horizontal.jpg

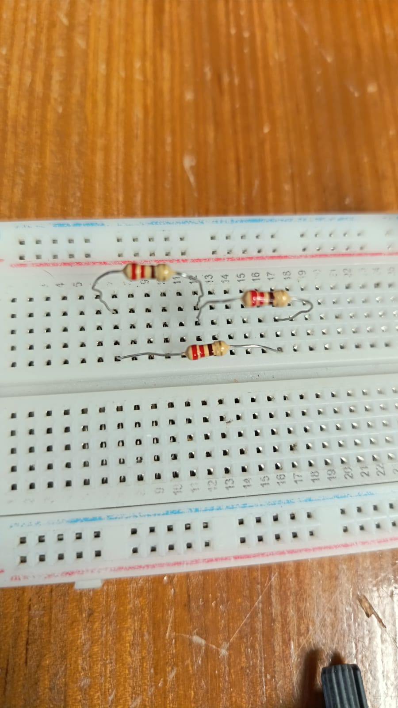
Documentacion/Talleres/Taller de electrónica/T2/pollo horizontal.jpg
