adysanchez-10/Grupo-4-oficial/Documentacion/Talleres/Taller de electrónica/T3/Cálculos T3.jpg

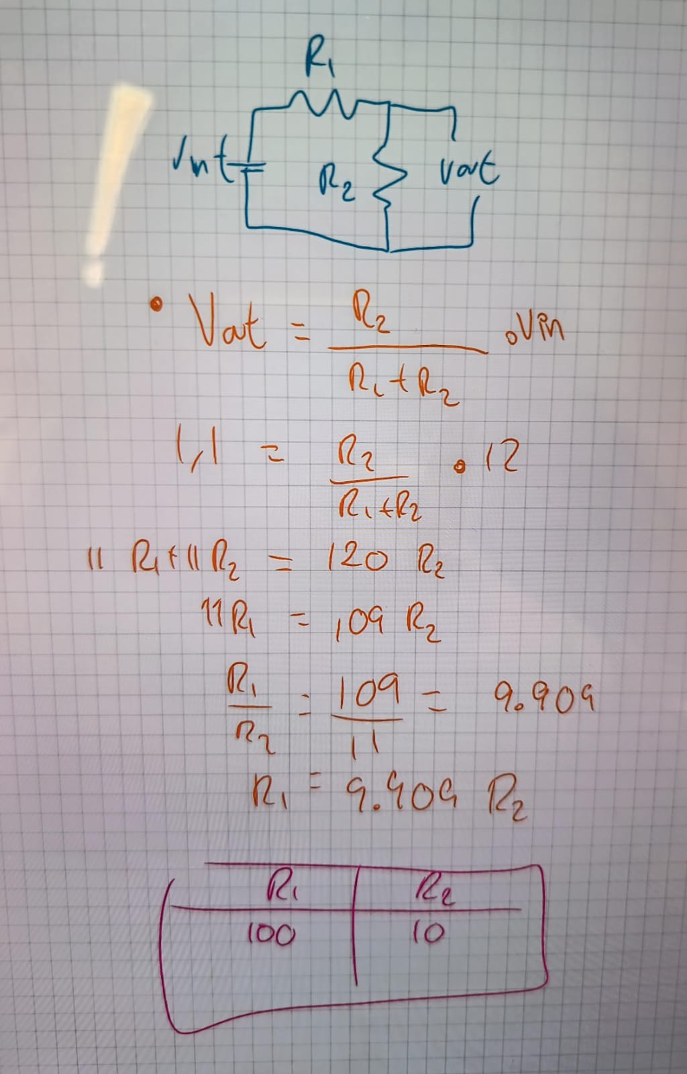
Documentacion/Talleres/Taller de electrónica/T3/Cálculos T3.jpg
