adysanchez-10/Grupo-4-oficial/Documentacion/Talleres/Taller 22.10.25/Ejemplo 2/Universal Joint Flange Drawing 1.pdf

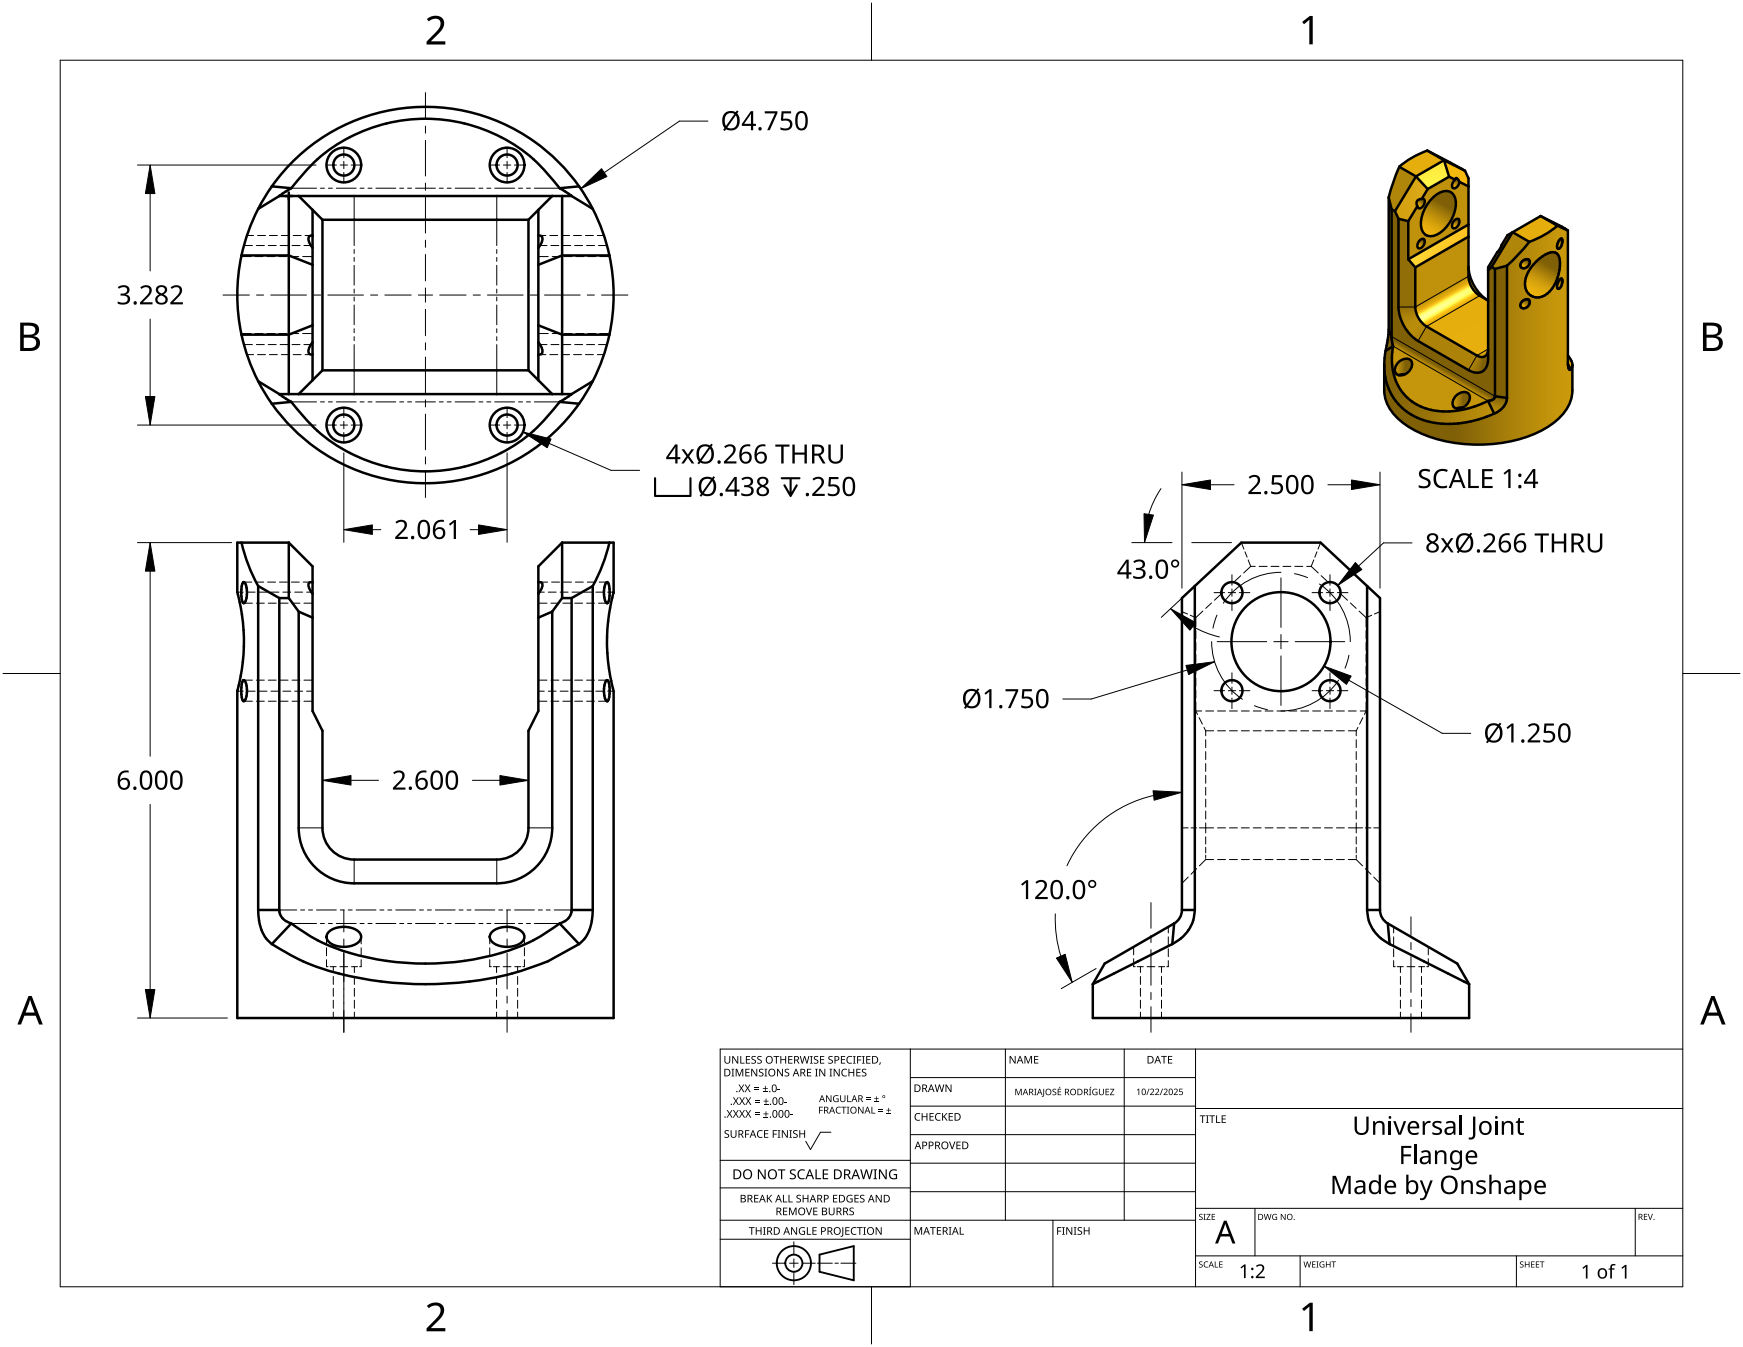
[picture p158: page 1]
