adysanchez-10/Grupo-4-oficial/Documentacion/Talleres/Taller 22.10.25/Ejemplo 2/Drive Sleeve Drawing.pdf

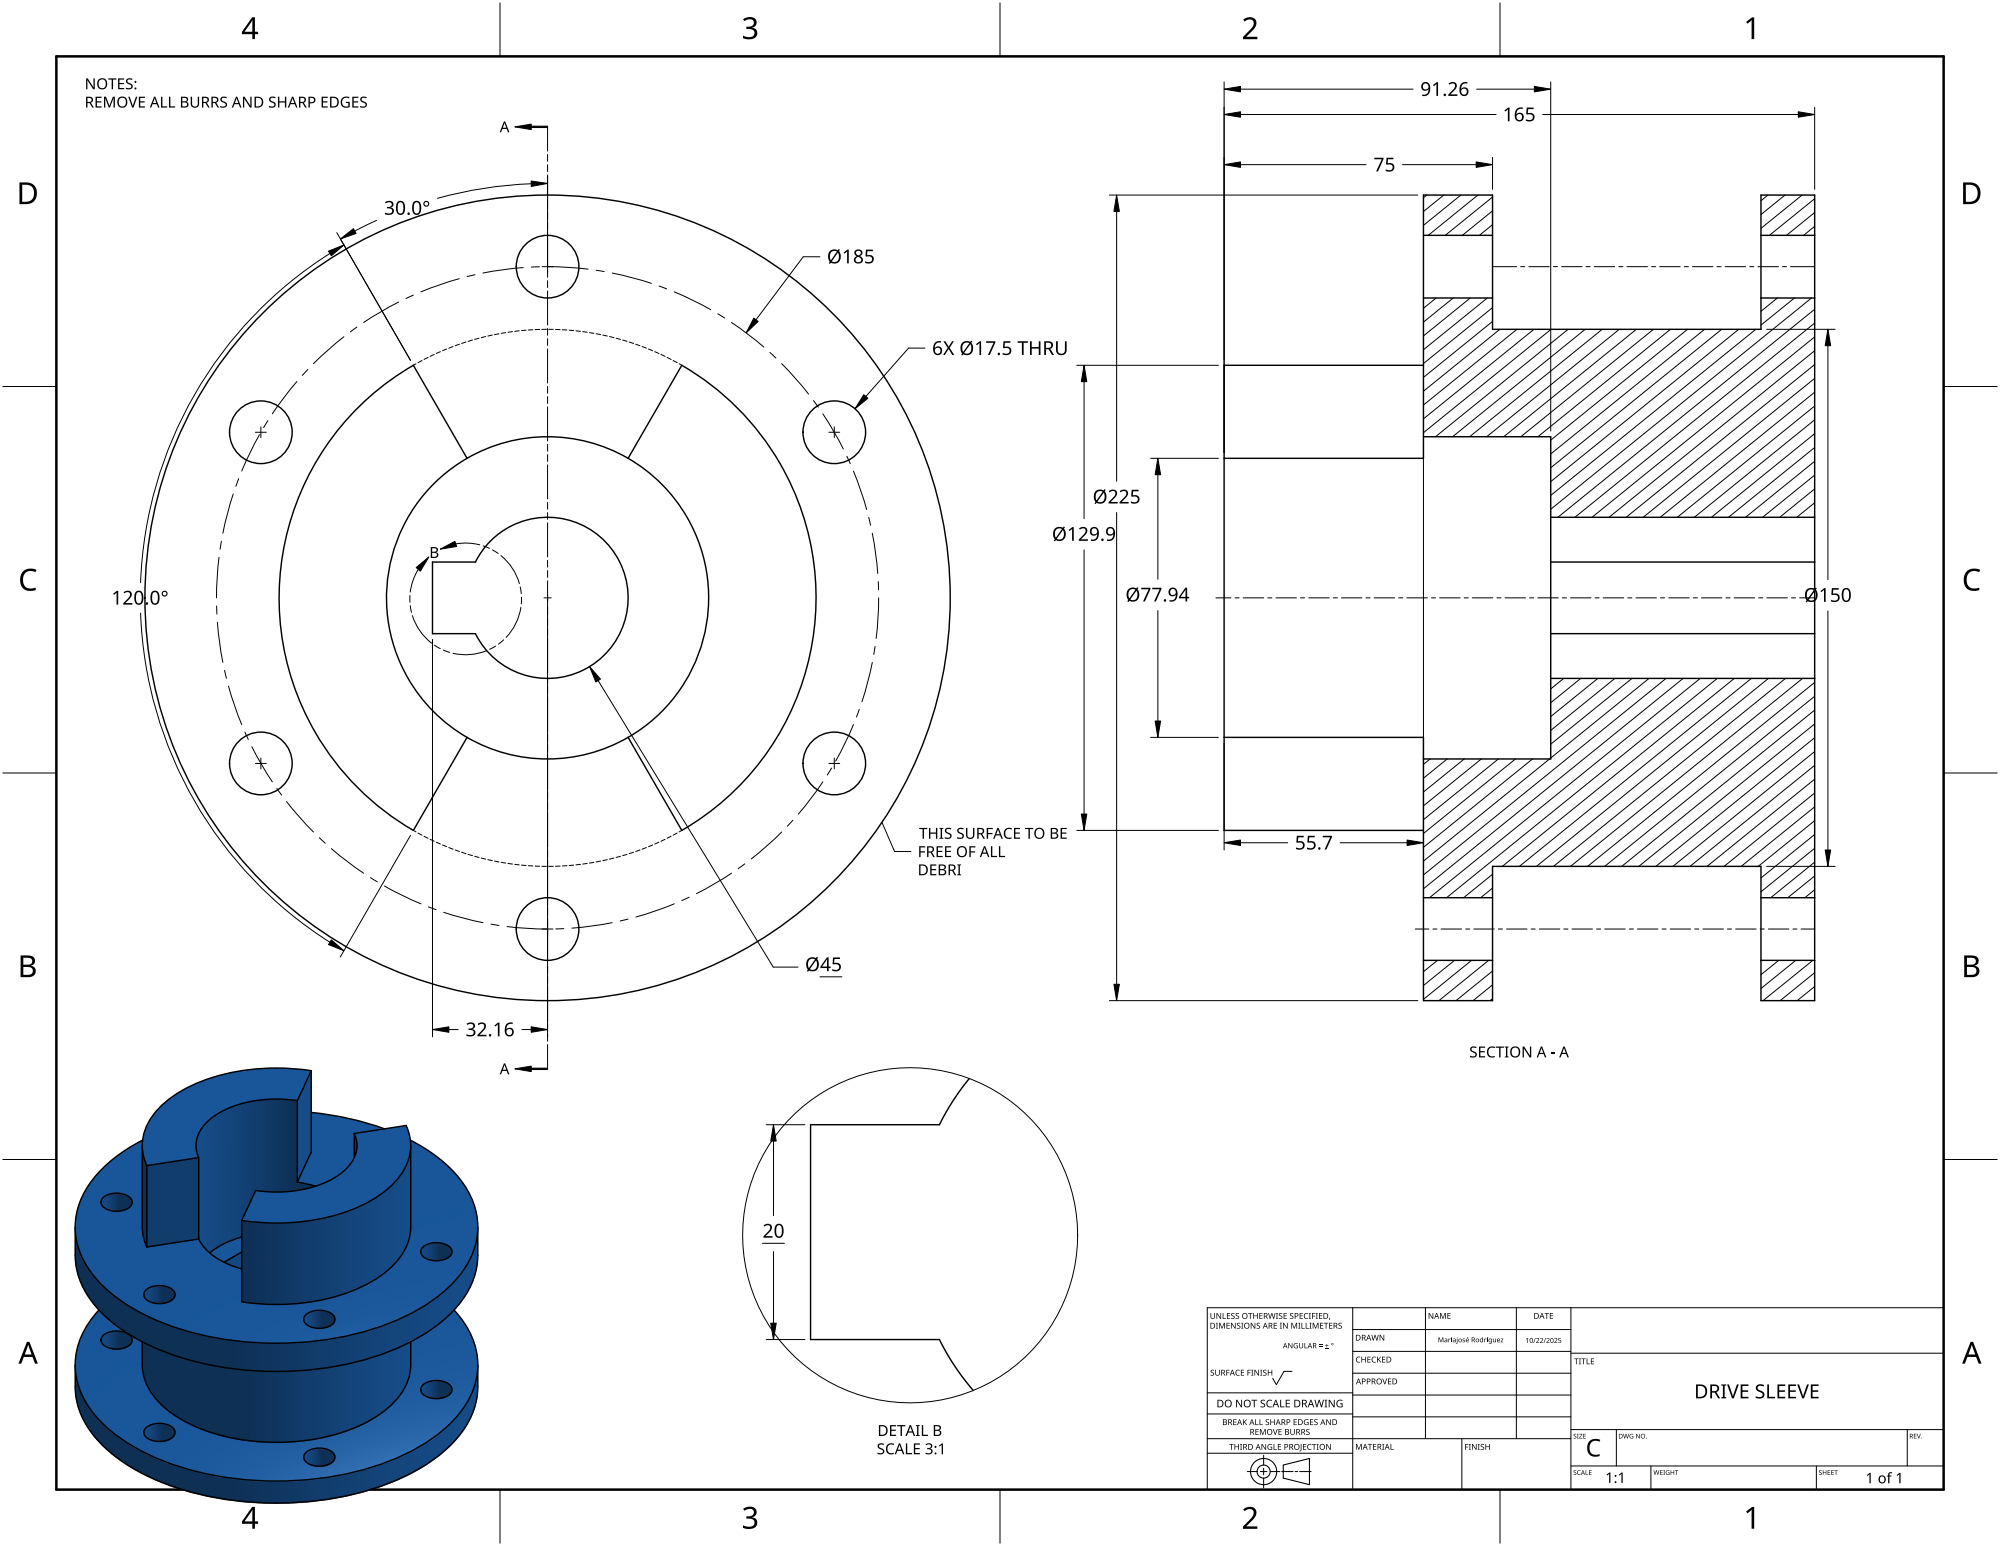
[picture p159: page 1]
